IvaylooTs/StarTracker/Docs/Hardware_reasearch/Day 25 - 14.08.md

Optimized the raspberry pi by removing 

systemd-analyze blame
systemd-analyze critical-chain
systemd-analyze

the fasterst optimization was removing this
  sudo systemctl disable NetworkManager-wait-online.service 
this sped up the boot time from ~11 seconds to ~ 5-6 seconds

  sudo systemctl status bluetooth
   sudo systemctl status hciuart
   sudo systemctl deactivate hciuart
   sudo systemctl disable bluetooth

 1334  sudo systemctl disable avahi-daemon
static ip
 1364  sudo systemctl status keyboard-setup.service
 1365  sudo systemctl status triggerhappy.s
 1366  sudo systemctl status triggerhappy
 1367  sudo systemctl status ModemManager.service 
 1368  sudo systemctl status avahi-daemon.s
 1369  sudo systemctl status avahi-daemon.service 
 1370  sudo systemctl status avahi-daemon
 1371  sudo systemctl status dphys-swapfil 1375  sudo systemctl disable rpi-eeprom-update.service 
 1376  sudo systemctl disable keyboard-setup.service 
e.service 
 1372  systemd-analyze 

 1432  sudo systemd-analyze blame
 1433  sudo systemd-analyze time
 1434  sudo cat /sys/kernel/debug/mmc0/ios
 1435  sudo nano /boot/firmware/config.txt 
 1436  reboot
 1437  sudo cat /sys/kernel/debug/mmc0/ios
 1438  sudo nano /boot/firmware/config.txt

other systems
disable_splash=1
boot_delay=0
initial_turbo=30
dtparam=audio=off
dtparam=spi=off
display_auto_detect=0
gpu_mem=16

dtparam=sd_overclock=100 - not used, didn't work.
