IvaylooTs/StarTracker/Docs/Hardware_reasearch/Day 7 - 27.07.md

No significant progress made that day.

Studying quaternions little -> https://eater.net/quaternions/
https://forums.unrealengine.com/t/how-to-use-quaternions/635199

Experimentation with Three.js for visualization of objects with quaternions, transfer information via web sockets.

```html
<!-- used version from day 8 28.07-->
<!DOCTYPE html>
<html>
<head>
<title>WebSocket Test</title>
<style>
	#messages {
		max-height: 400px;
		overflow-y: auto;
		border: 1px solid #ccc;
		padding: 10px;
		font-family: sans-serif;
	}
	#three-container {
		position: absolute;
		top: 0;
		left: 0;
		width: 50vw; /* Half width */
		height: 50vh; /* Half height */
		background: white;
		overflow: hidden;
	}
</style>
</head>
<body>
<h1>Messages from Raspberry Pi:</h1>

<script>
	const ws = new WebSocket('ws://192.168.55.160:6789');
	ws.onopen = () => console.log('WebSocket connected');
	ws.onmessage = function(event) {
		const messageDiv = document.getElementById('messages');
		const p = document.createElement('p');
		p.textContent = event.data;
		messageDiv.appendChild(p);
		messageDiv.scrollTop = messageDiv.scrollHeight;
	};
	
	ws.onclose = () => console.log('WebSocket closed');
	ws.onerror = (err) => console.error('WebSocket error:', err);
</script>
</body>
</html>
```
