IvaylooTs/StarTracker/backups/First interface/README.md

# Day 9

Finished the front UI 
 - cannot push custom commands from terminal CLI, needs custom buttons
 - 3d visualization
 - quaternion display
 - received info displayed
 - camera live

Raspberry Pi server
 - get data from sensor I2C (no library, direct connection)
 - calibrates on hardware level
 - gets camera live video (VGA quality - fast video, Full HD - slow video)
