IvaylooTs/StarTracker/CASSI_Website/Team.JPG

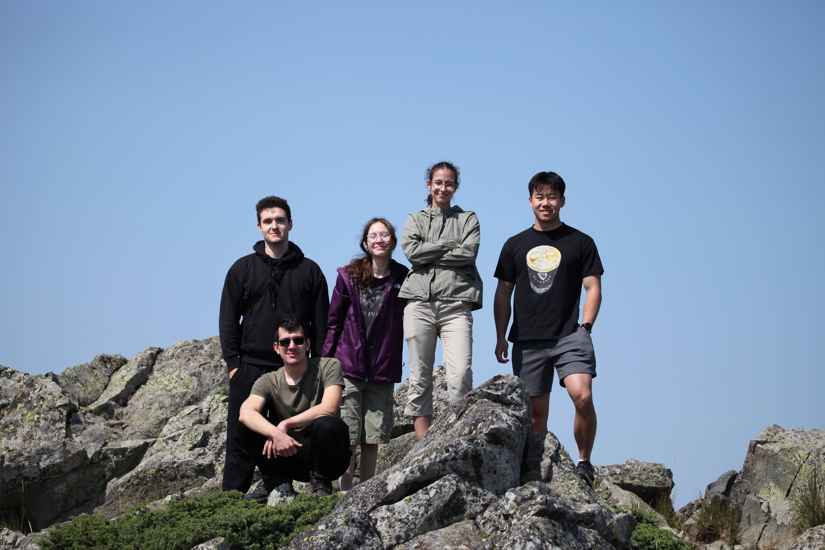
CASSI_Website/Team.JPG
