IvaylooTs/StarTracker/DeveloperUI/Images/wbackground.jpg

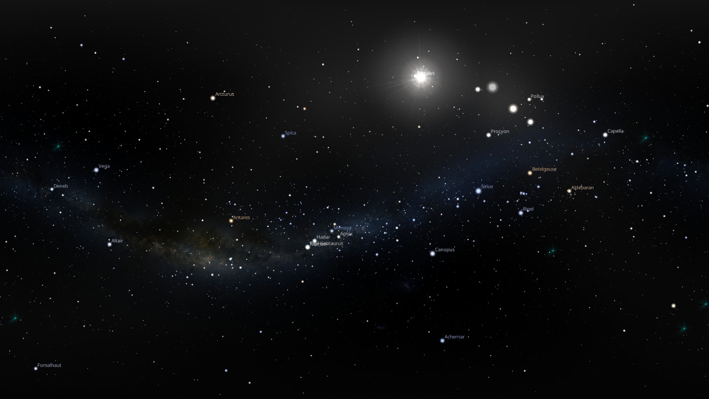
DeveloperUI/Images/wbackground.jpg
