IvaylooTs/StarTracker/DeveloperUI/Pasted image.png

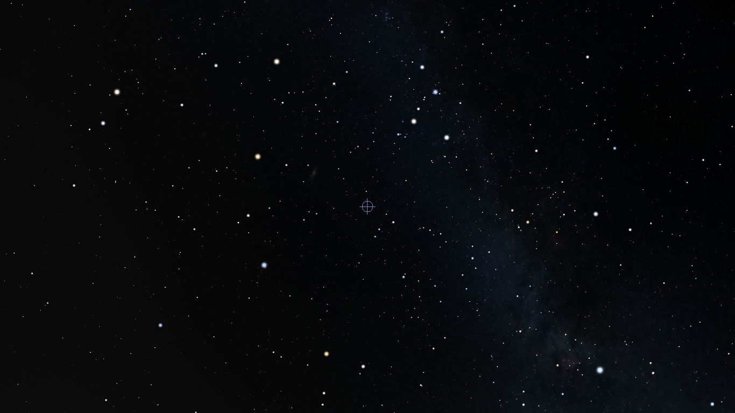
DeveloperUI/Pasted image.png
