IvaylooTs/StarTracker/Docs/Diagrams/BootCycle.drawio(2).png

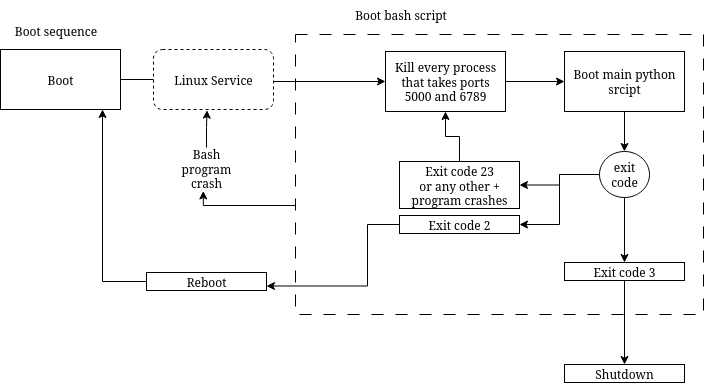
Docs/Diagrams/BootCycle.drawio(2).png
