IvaylooTs/StarTracker/Docs/Diagrams/concept_IMUbootSequence.drawio.png

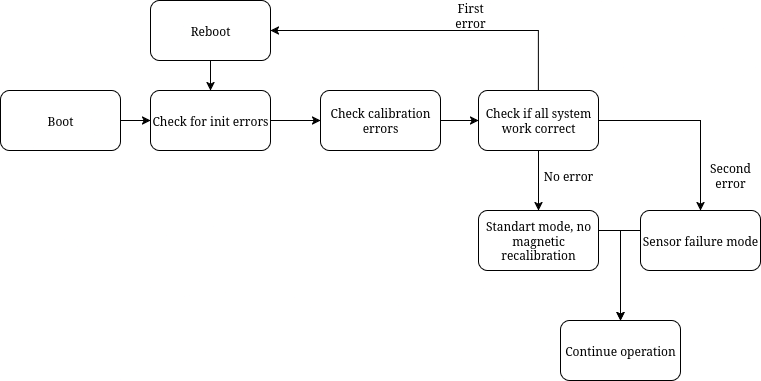
Docs/Diagrams/concept_IMUbootSequence.drawio.png
