IvaylooTs/StarTracker/Docs/Diagrams/Hardware-Diagram.drawio.png

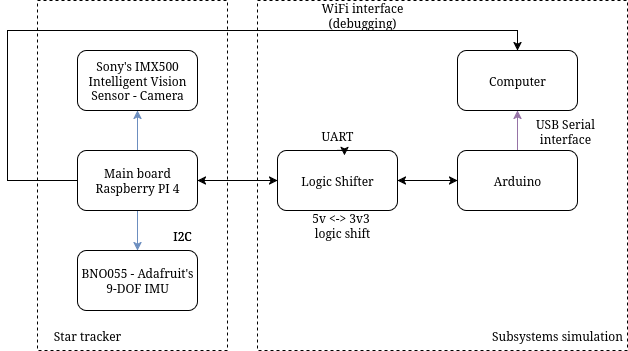
Docs/Diagrams/Hardware-Diagram.drawio.png
