IvaylooTs/StarTracker/Docs/Diagrams/HardwareSystem.drawio.png

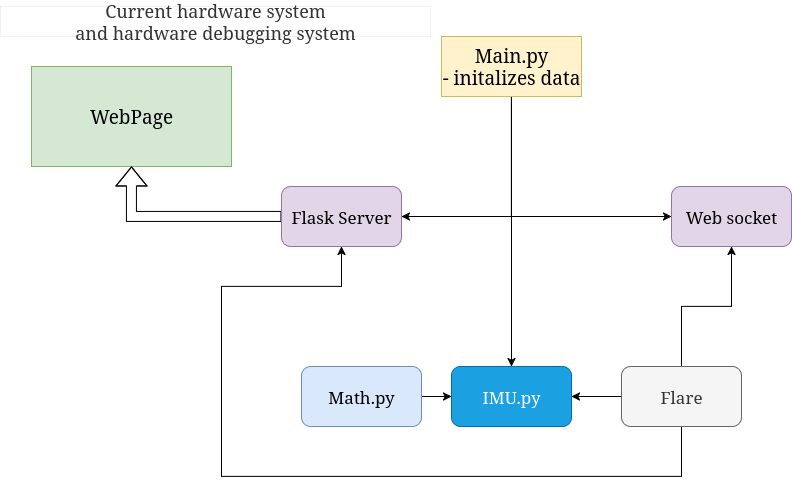
Docs/Diagrams/HardwareSystem.drawio.png
