IvaylooTs/StarTracker/Docs/Hardware_reasearch/additional images/Raspberry Pi Camera connector.png

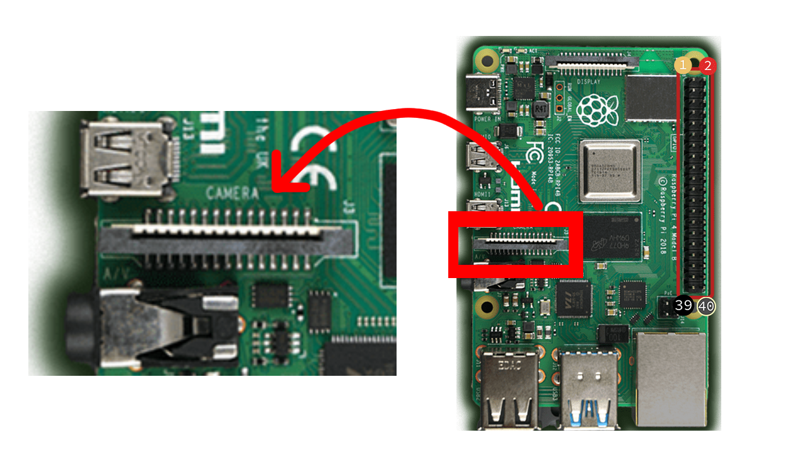
Docs/Hardware_reasearch/additional images/Raspberry Pi Camera connector.png
