IvaylooTs/StarTracker/Docs/Hardware_reasearch/ConceptUI.drawio.png

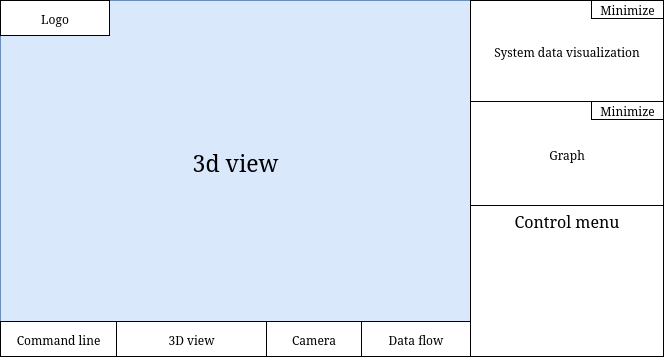
Docs/Hardware_reasearch/ConceptUI.drawio.png
