IvaylooTs/StarTracker/Docs/Hardware_reasearch/Figure_1(1).png

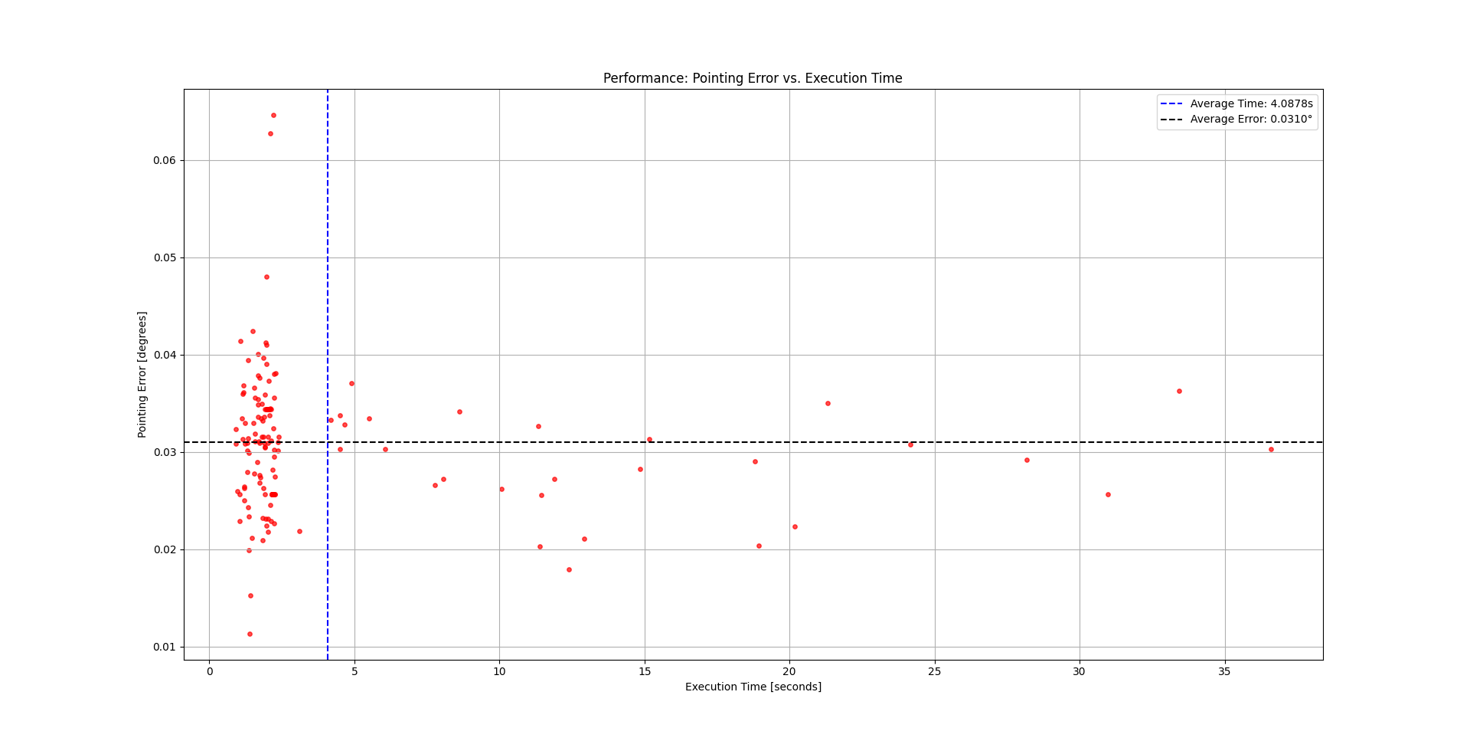
Docs/Hardware_reasearch/Figure_1(1).png
