IvaylooTs/StarTracker/Docs/Hardware_reasearch/Pasted image 20250724163324.png

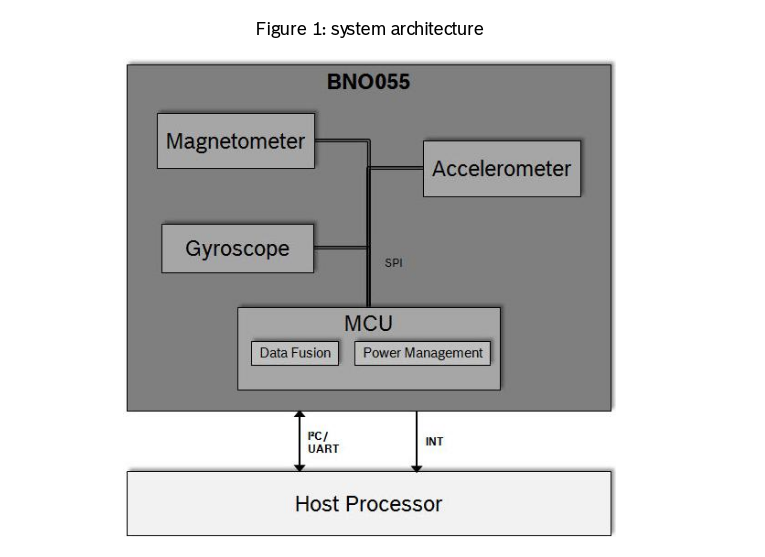
Docs/Hardware_reasearch/Pasted image 20250724163324.png
