IvaylooTs/StarTracker/Docs/Hardware_reasearch/Pasted image 20250725143316.png

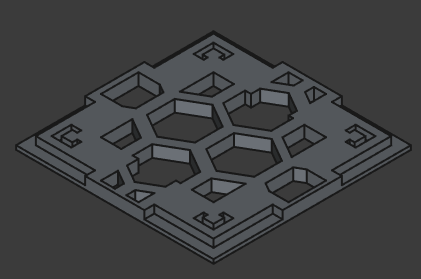
Docs/Hardware_reasearch/Pasted image 20250725143316.png
