IvaylooTs/StarTracker/Docs/Hardware_reasearch/Pasted image 20250729213933.png

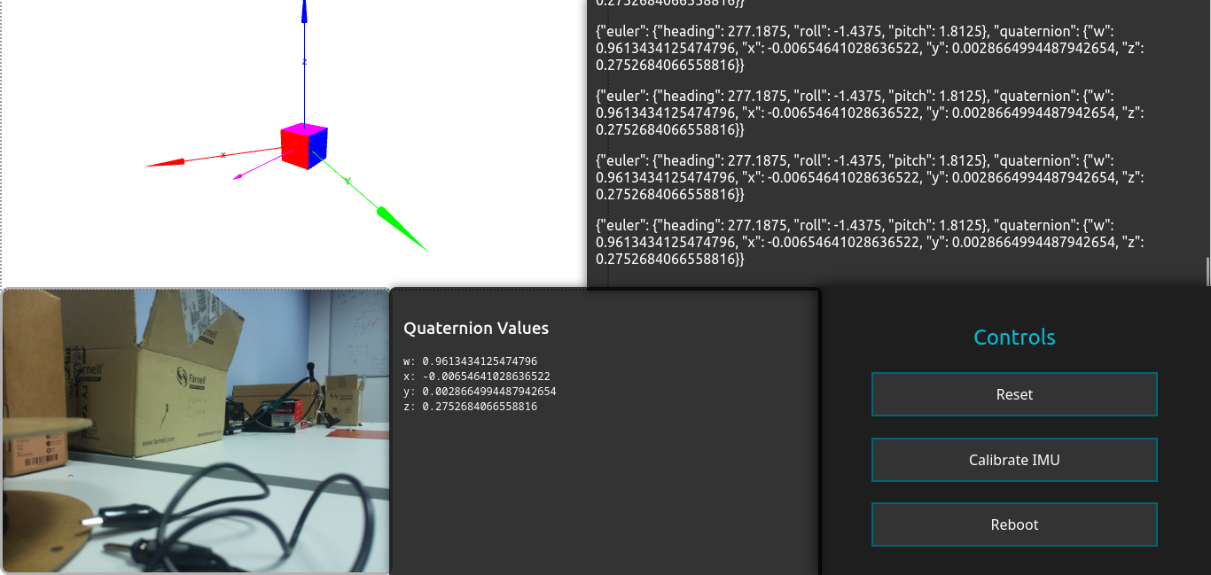
Docs/Hardware_reasearch/Pasted image 20250729213933.png
