IvaylooTs/StarTracker/Docs/Hardware_reasearch/Pasted image 20250731134919.png

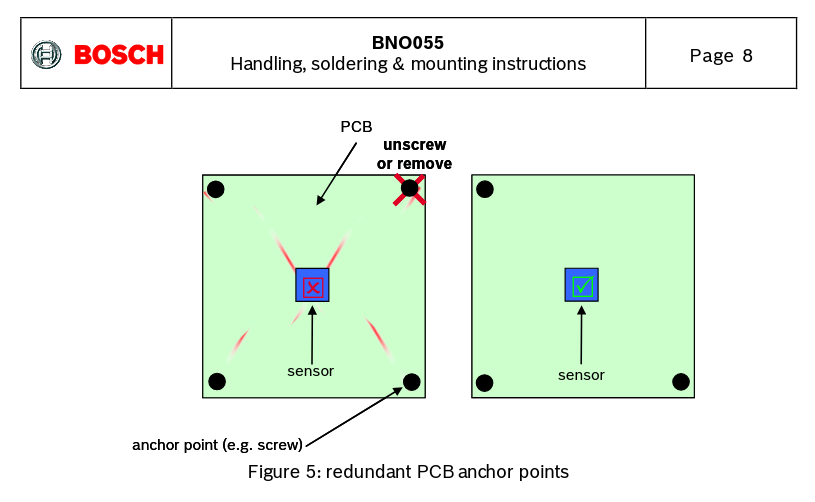
Docs/Hardware_reasearch/Pasted image 20250731134919.png
