IvaylooTs/StarTracker/Docs/Hardware_reasearch/Pasted image 20250815011902.png

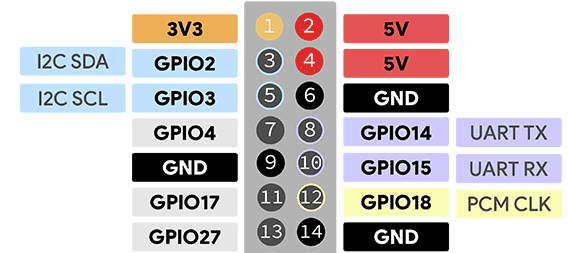
Docs/Hardware_reasearch/Pasted image 20250815011902.png
