IvaylooTs/StarTracker/Docs/Hardware_reasearch/Pasted image 20250816113234.png

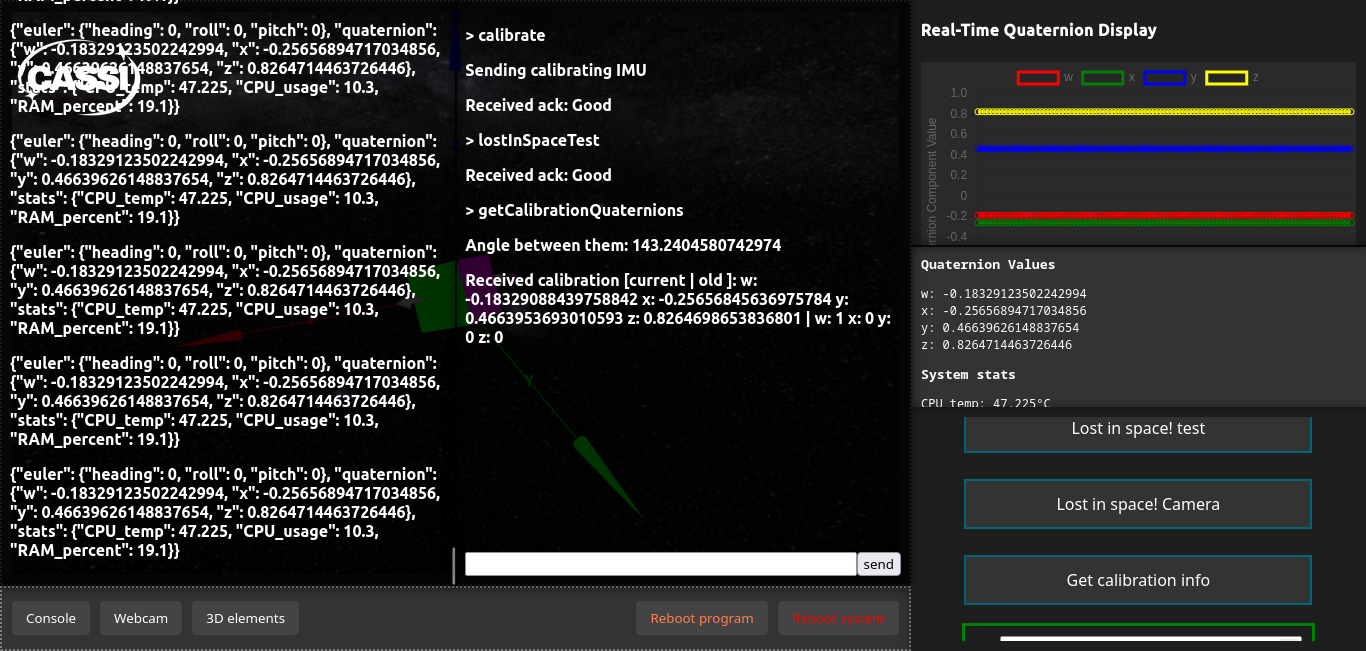
Docs/Hardware_reasearch/Pasted image 20250816113234.png
