IvaylooTs/StarTracker/Docs/Hardware_reasearch/Pasted image 20250816114603.png

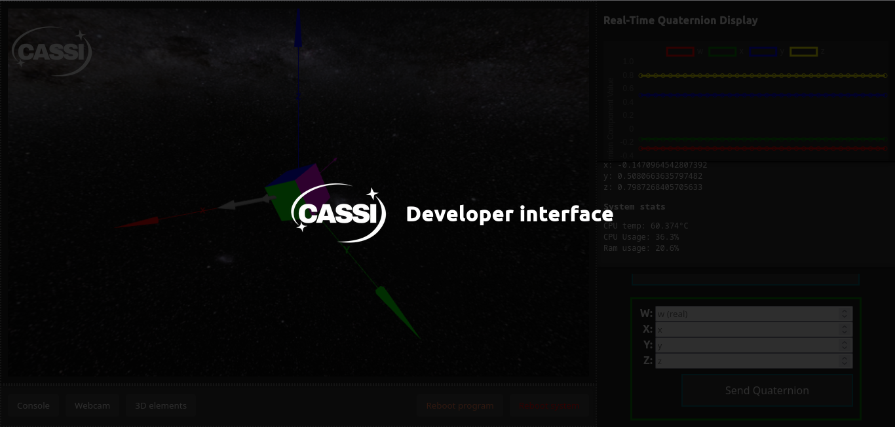
Docs/Hardware_reasearch/Pasted image 20250816114603.png
