IvaylooTs/StarTracker/Docs/Hardware_reasearch/Pasted image 20250816114728.png

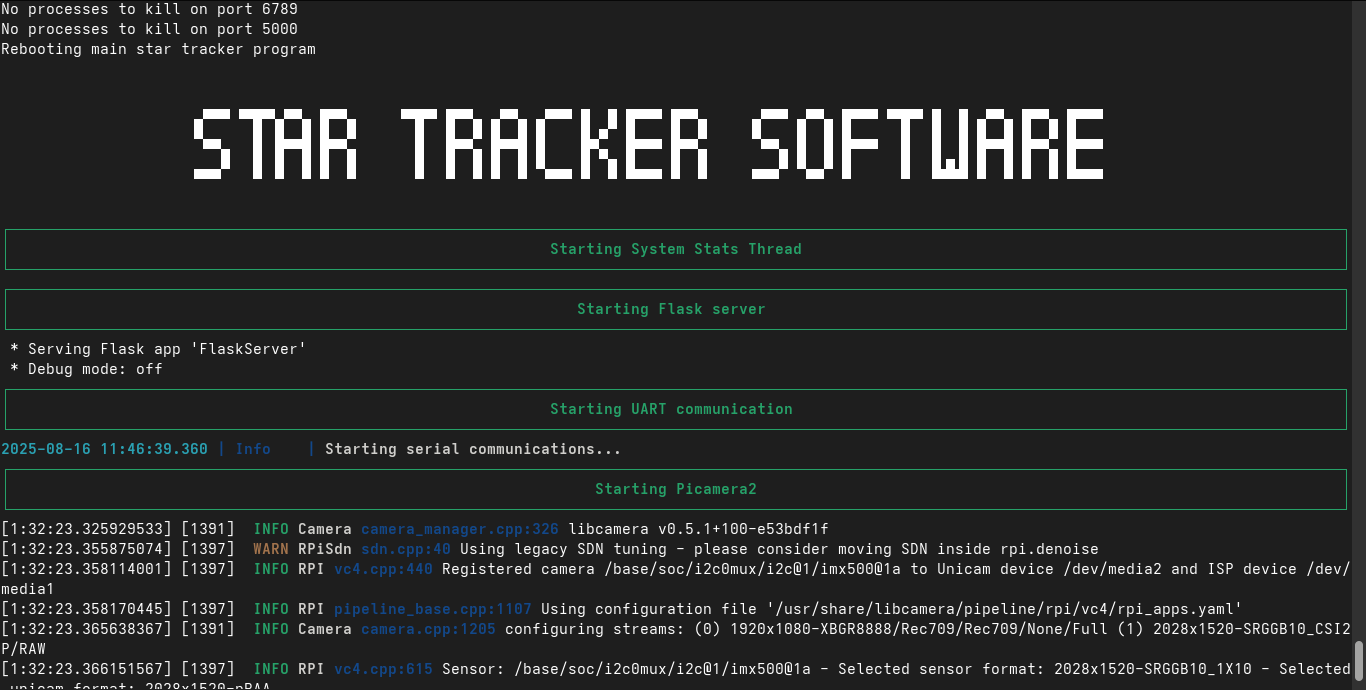
Docs/Hardware_reasearch/Pasted image 20250816114728.png
