IvaylooTs/StarTracker/Docs/Hardware_reasearch/Pasted image 20250816114743.png

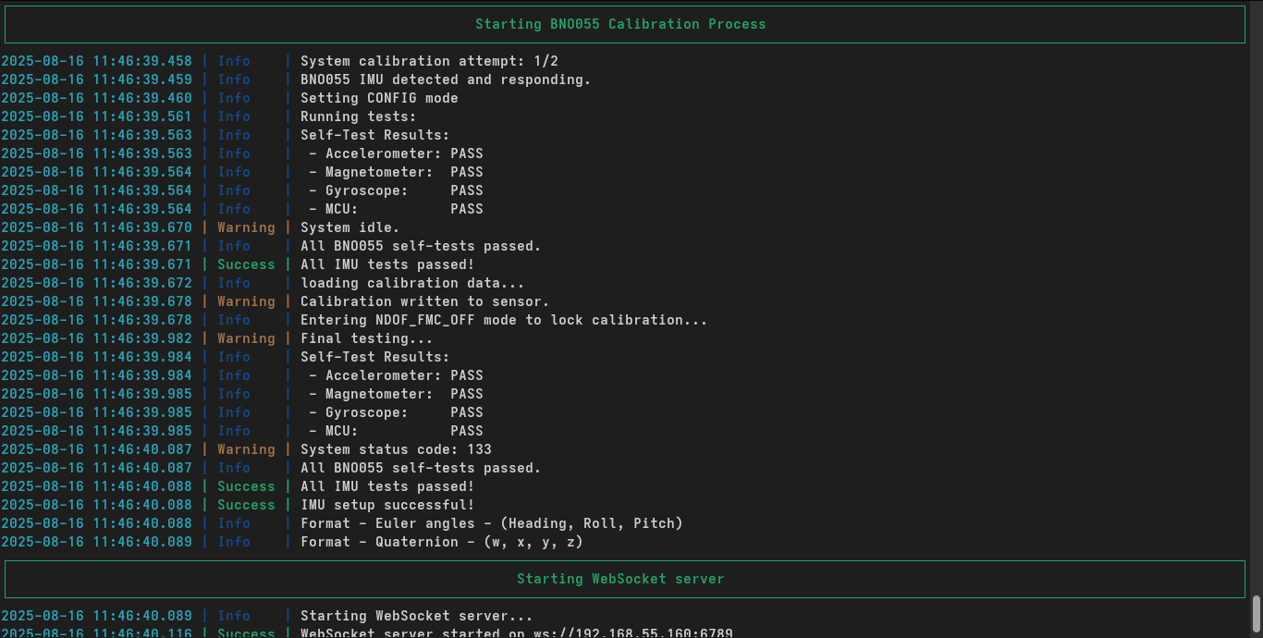
Docs/Hardware_reasearch/Pasted image 20250816114743.png
