IvaylooTs/StarTracker/Docs/Hardware_reasearch/Pasted image 20250816114801.png

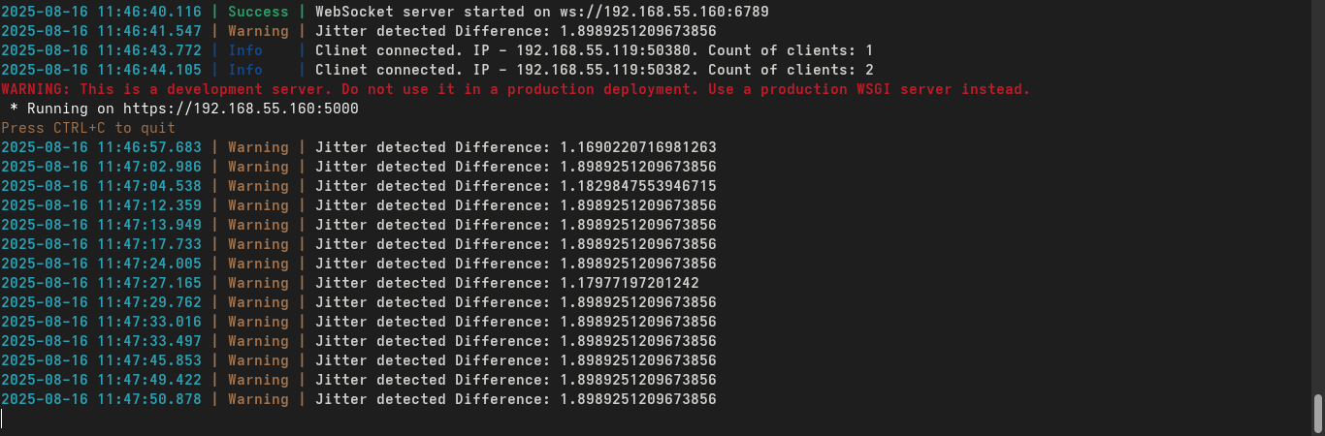
Docs/Hardware_reasearch/Pasted image 20250816114801.png
