IvaylooTs/StarTracker/Docs/Hardware_reasearch/Pasted image 20250816201824.png

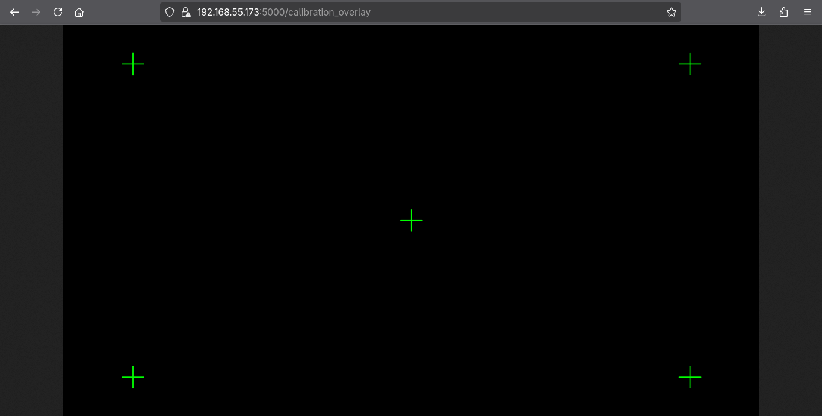
Docs/Hardware_reasearch/Pasted image 20250816201824.png
