IvaylooTs/StarTracker/Docs/Hardware_reasearch/Pasted image 20250816201958.png

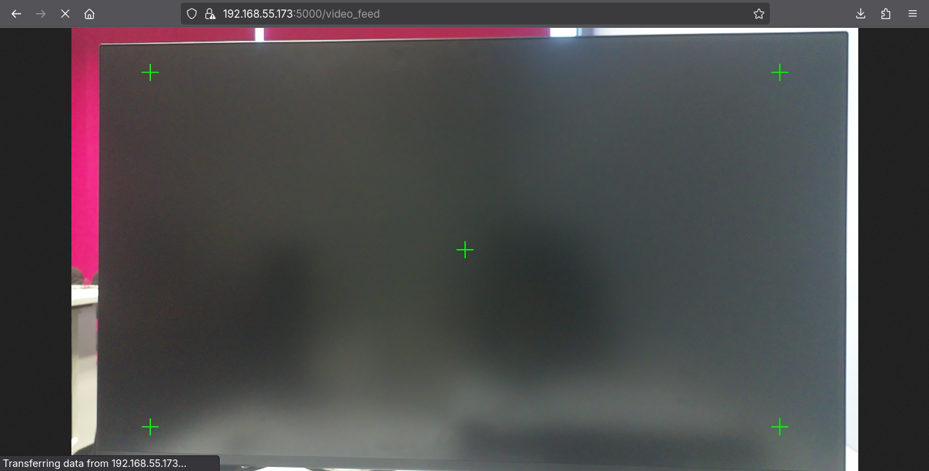
Docs/Hardware_reasearch/Pasted image 20250816201958.png
