IvaylooTs/StarTracker/Docs/Hardware_reasearch/Pasted image 20250816202409.png

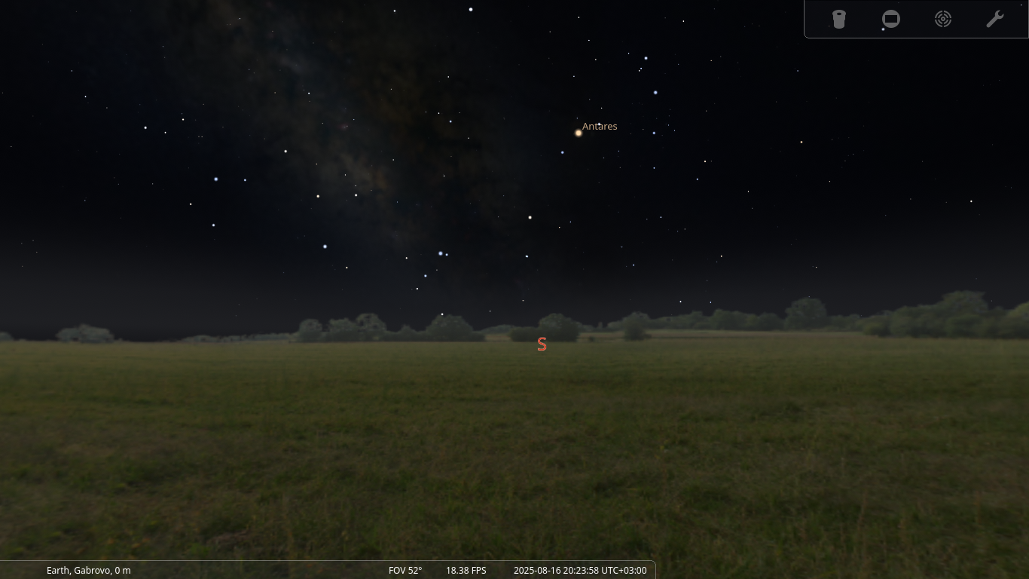
Docs/Hardware_reasearch/Pasted image 20250816202409.png
