IvaylooTs/StarTracker/Docs/Hardware_reasearch/Pasted image 20250816202426.png

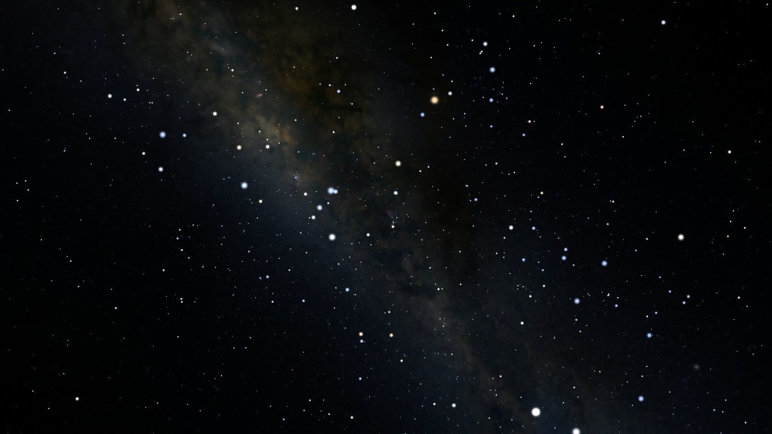
Docs/Hardware_reasearch/Pasted image 20250816202426.png
