IvaylooTs/StarTracker/Docs/Hardware_reasearch/Screenshot 2025-07-29 at 13-58-42 Three.js Cube with Arrow.png

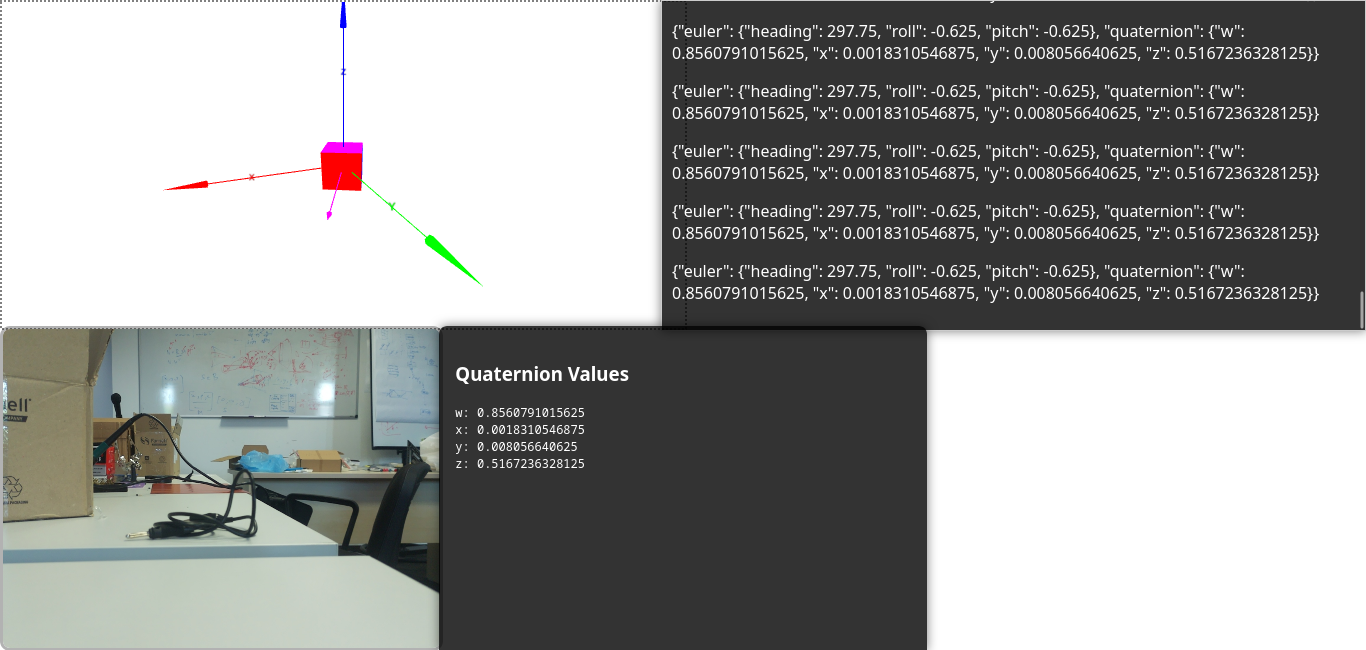
Docs/Hardware_reasearch/Screenshot 2025-07-29 at 13-58-42 Three.js Cube with Arrow.png
