IvaylooTs/StarTracker/Docs/Hardware_reasearch/Screenshot From 2025-07-31 18-01-20.png

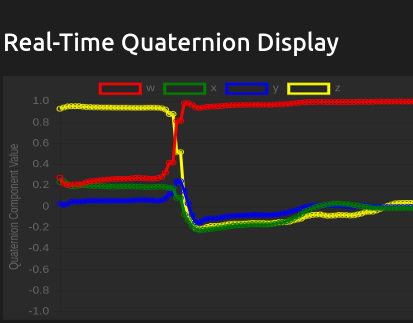
Docs/Hardware_reasearch/Screenshot From 2025-07-31 18-01-20.png
