IvaylooTs/StarTracker/Ivostuff/stars_identified.png

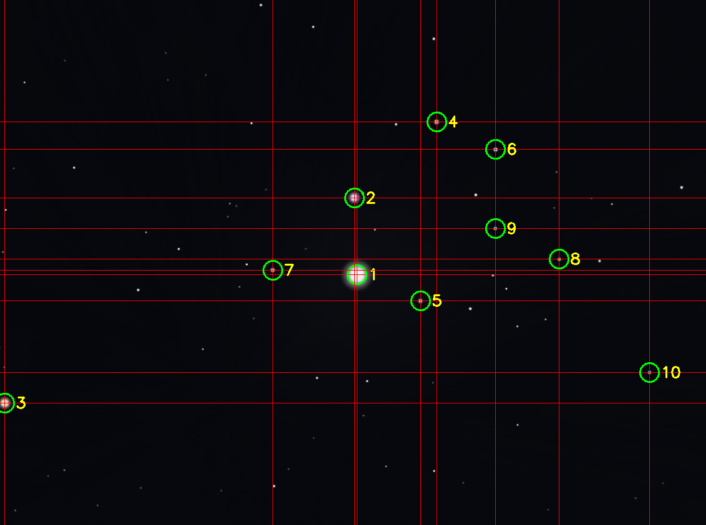
Ivostuff/stars_identified.png
