IvaylooTs/StarTracker/src/digital_twin/script_images/five.png

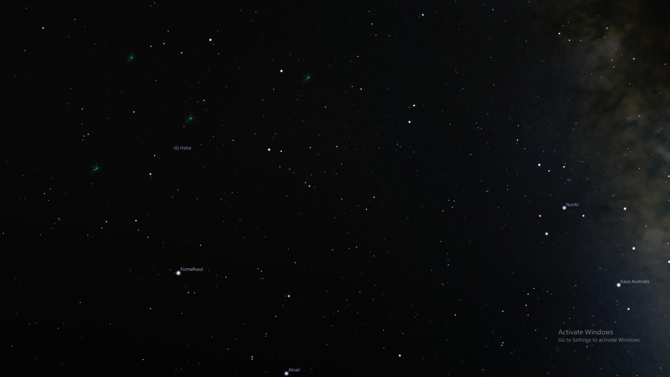
src/digital_twin/script_images/five.png
