IvaylooTs/StarTracker/src/digital_twin/script_images/four.png

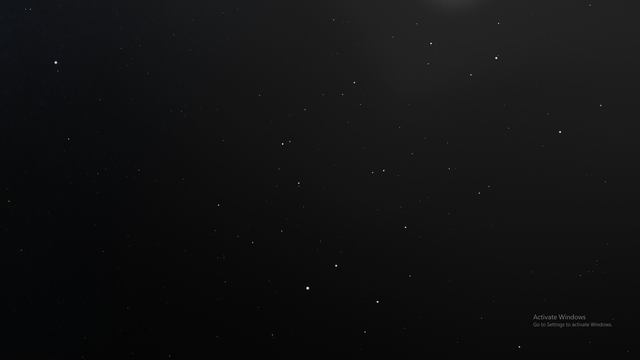
src/digital_twin/script_images/four.png
