IvaylooTs/StarTracker/src/digital_twin/script_images/im2.png

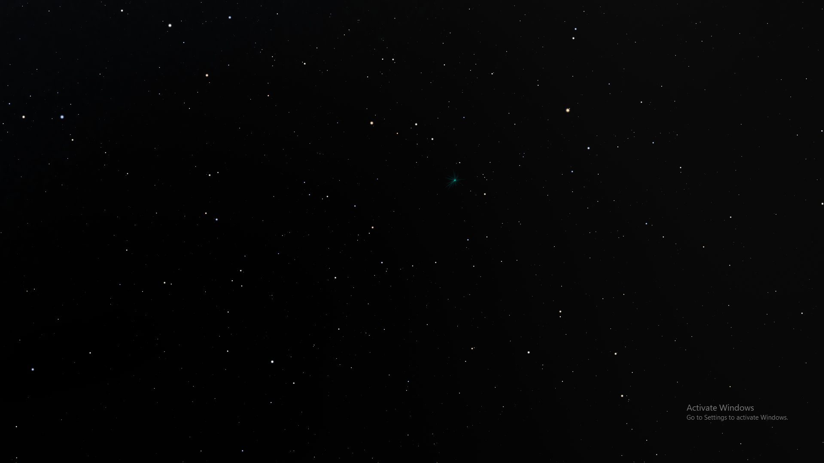
src/digital_twin/script_images/im2.png
