IvaylooTs/StarTracker/src/digital_twin/script_images/im3.png

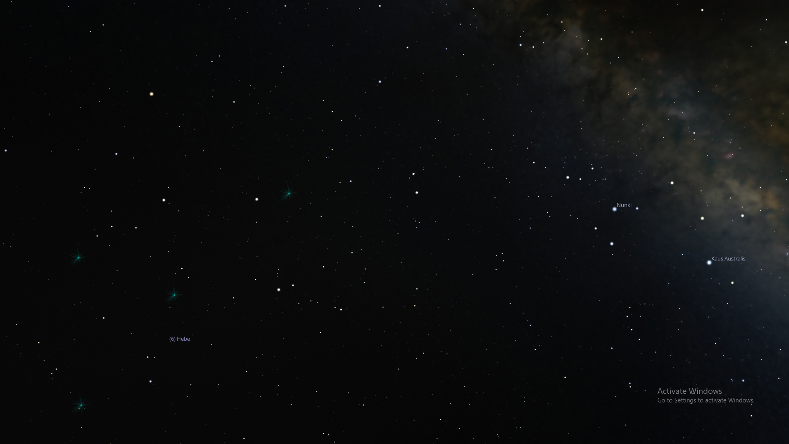
src/digital_twin/script_images/im3.png
