IvaylooTs/StarTracker/src/digital_twin/script_images/image copy.png

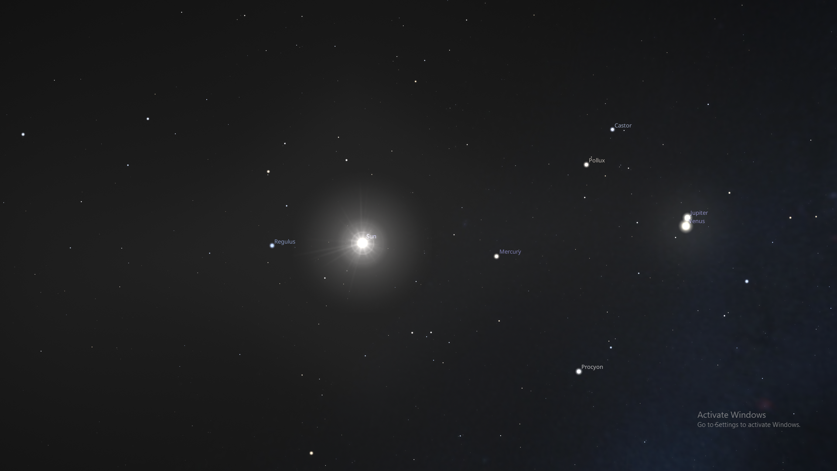
src/digital_twin/script_images/image copy.png
