IvaylooTs/StarTracker/src/digital_twin/script_images/image.png

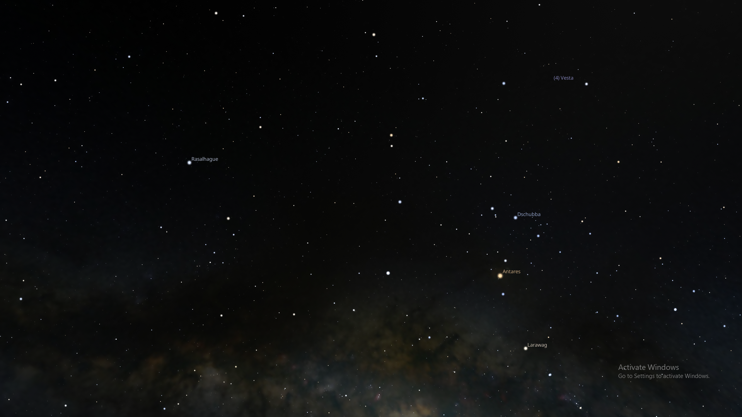
src/digital_twin/script_images/image.png
