IvaylooTs/StarTracker/src/digital_twin/script_images/mars.png

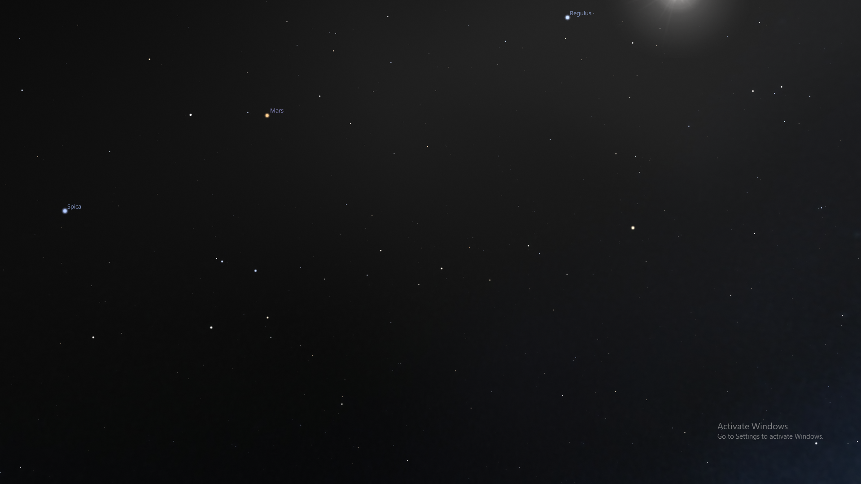
src/digital_twin/script_images/mars.png
