IvaylooTs/StarTracker/src/digital_twin/script_images/one.png

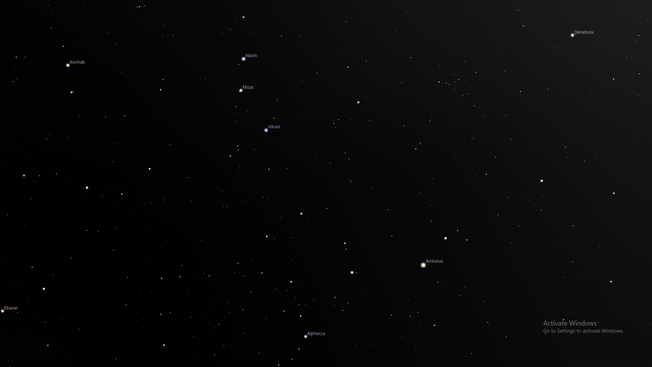
src/digital_twin/script_images/one.png
