IvaylooTs/StarTracker/src/digital_twin/script_images/sat2.png

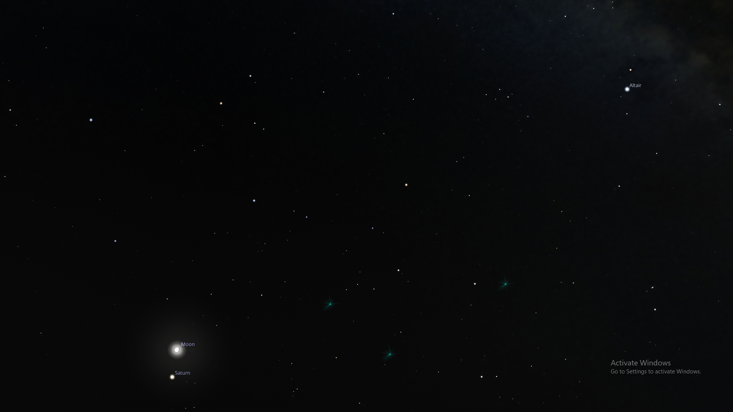
src/digital_twin/script_images/sat2.png
