IvaylooTs/StarTracker/src/digital_twin/script_images/saturn.png

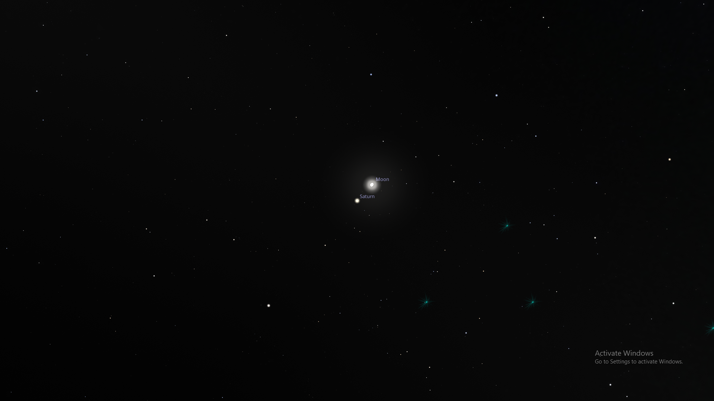
src/digital_twin/script_images/saturn.png
