IvaylooTs/StarTracker/src/digital_twin/script_images/sun.png

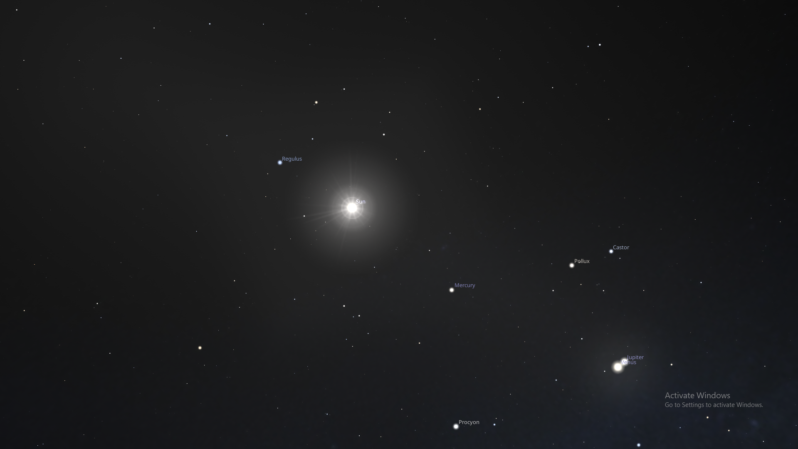
src/digital_twin/script_images/sun.png
