IvaylooTs/StarTracker/src/digital_twin/script_images/three.png

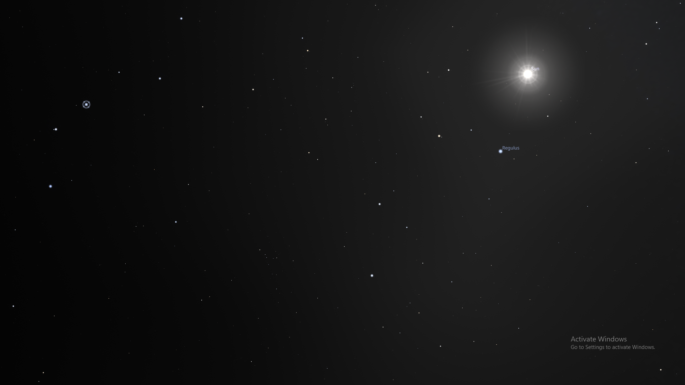
src/digital_twin/script_images/three.png
