IvaylooTs/StarTracker/src/digital_twin/script_images/two.png

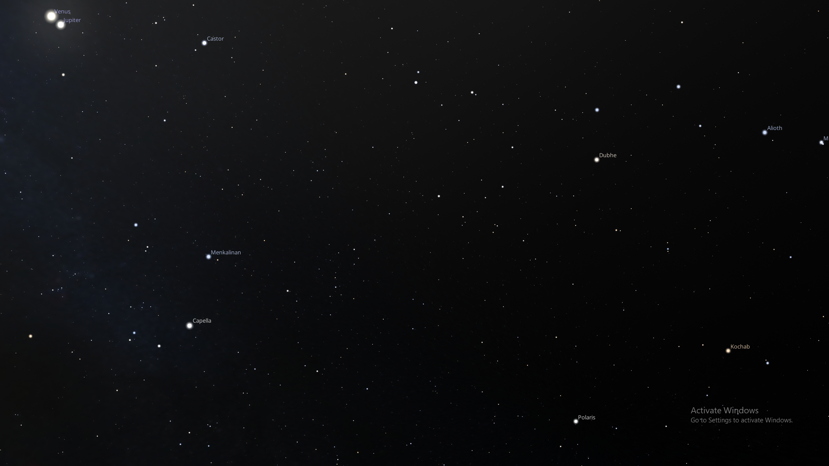
src/digital_twin/script_images/two.png
