IvaylooTs/StarTracker/src/digital_twin/script_images/vertical_045_deg001.png

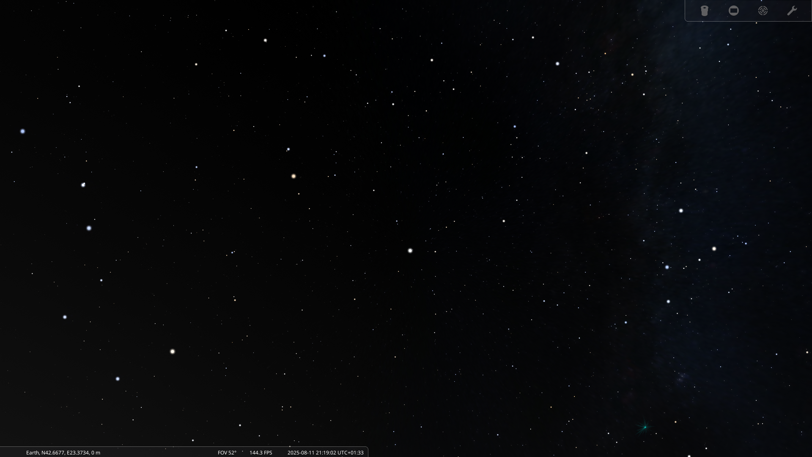
src/digital_twin/script_images/vertical_045_deg001.png
