IvaylooTs/StarTracker/src/digital_twin/script_images/vertical_090_deg001.png

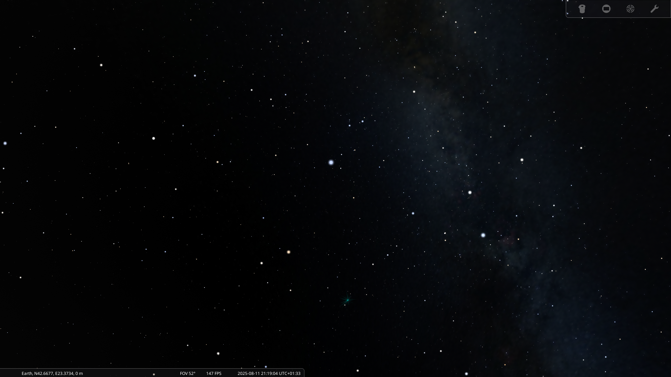
src/digital_twin/script_images/vertical_090_deg001.png
