IvaylooTs/StarTracker/src/digital_twin/script_images/vertical_270_deg001.png

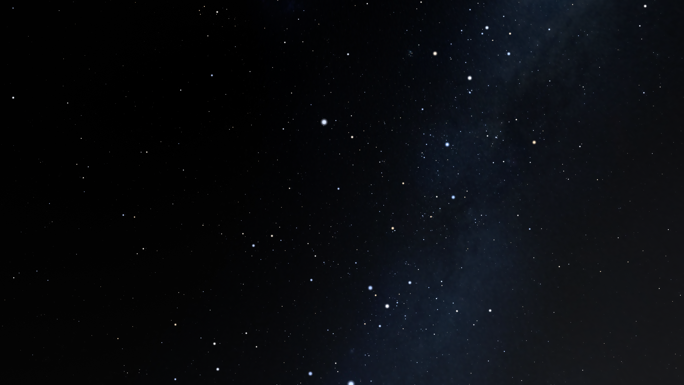
src/digital_twin/script_images/vertical_270_deg001.png
