IvaylooTs/StarTracker/src/digital_twin/script_images/vertical_315_deg001.png

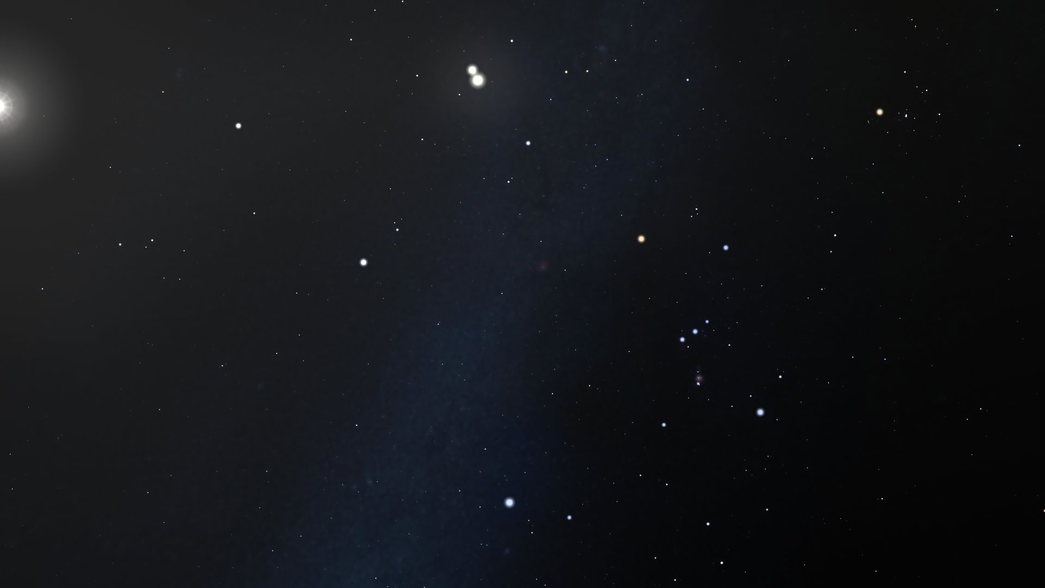
src/digital_twin/script_images/vertical_315_deg001.png
