IvaylooTs/StarTracker/src/digital_twin/stars_identified.png

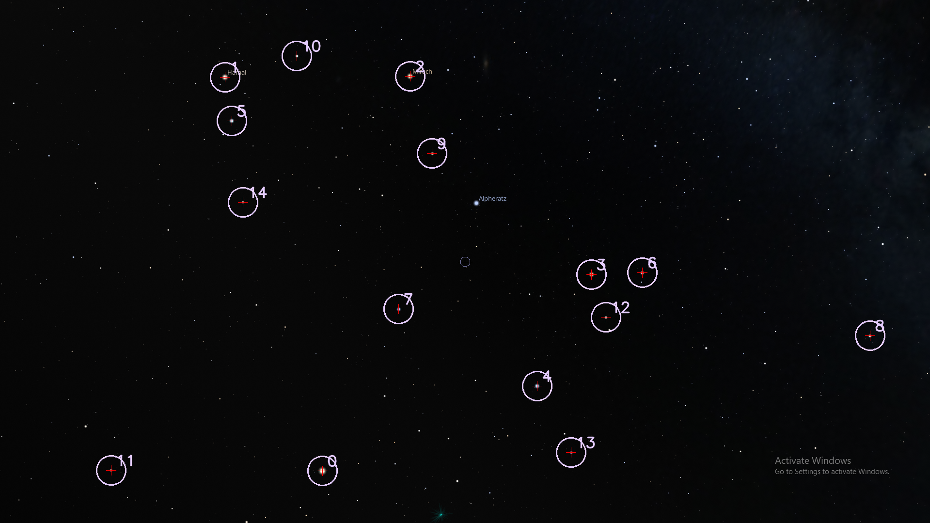
src/digital_twin/stars_identified.png
