IvaylooTs/StarTracker/src/star_tracking/image_processing/stars_identified.png

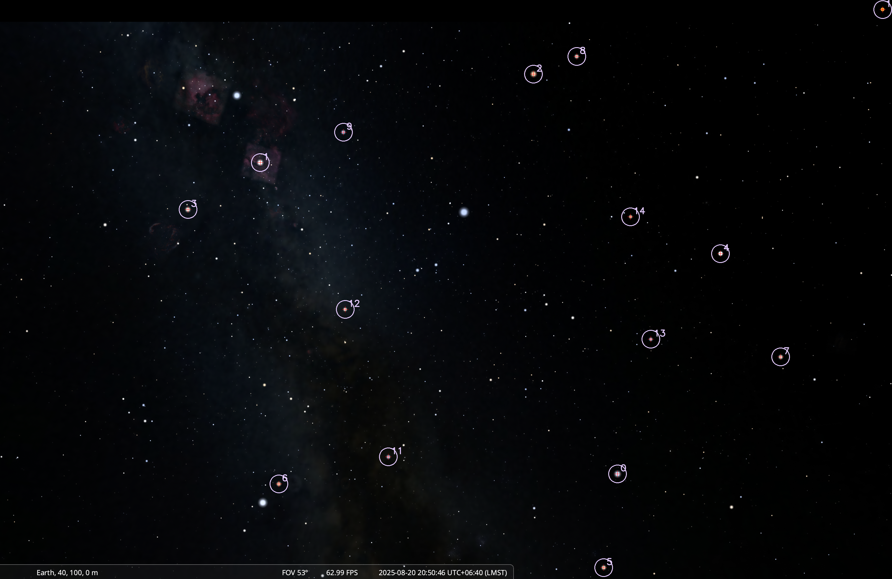
src/star_tracking/image_processing/stars_identified.png
