IvaylooTs/StarTracker/backups/test images from the final/README.md

# info

Some pictures taken on from the star tracker. 
Here you can find some from:
- testing
- presentation
- calibration
