IvaylooTs/StarTracker/Docs/Diagrams/Tests.drawio.png

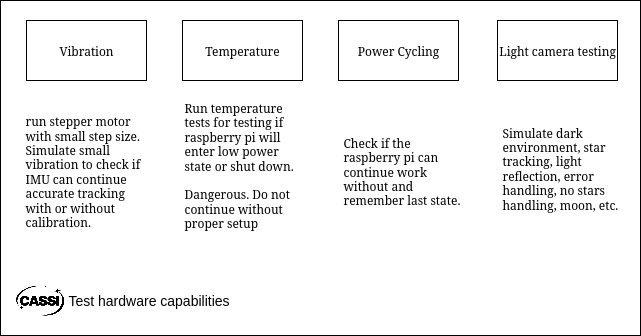
Docs/Diagrams/Tests.drawio.png
