IvaylooTs/StarTracker/src/digital_twin/script_images/test1.png

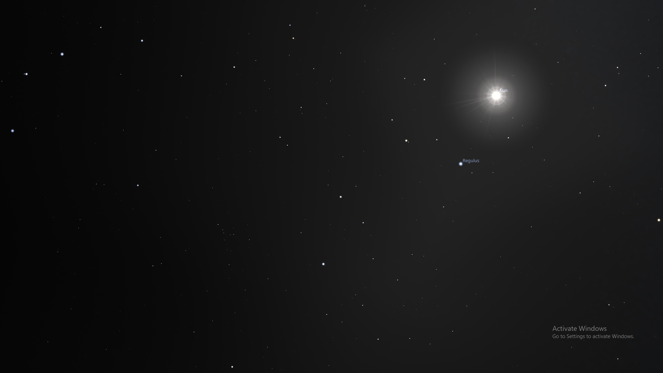
src/digital_twin/script_images/test1.png
