IvaylooTs/StarTracker/src/digital_twin/script_images/test2.png

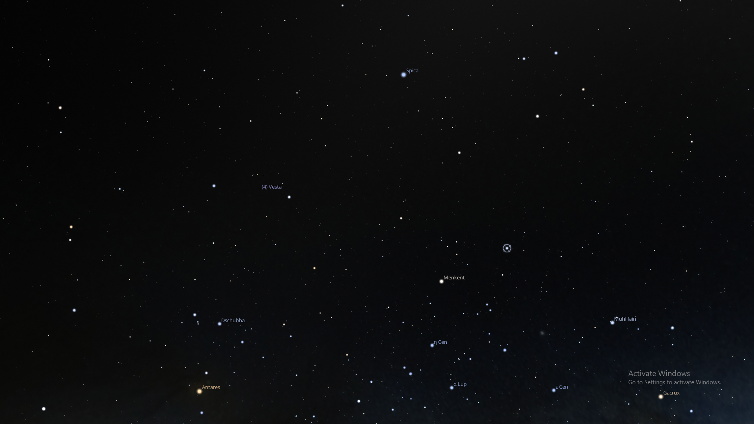
src/digital_twin/script_images/test2.png
