IvaylooTs/StarTracker/src/digital_twin/test_images/cat3.png

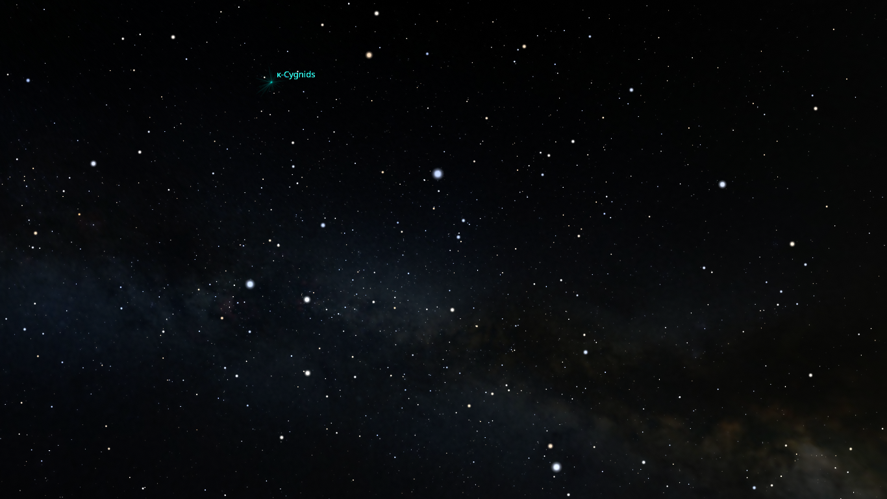
src/digital_twin/test_images/cat3.png
