IvaylooTs/StarTracker/src/digital_twin/test_images/cat5.png

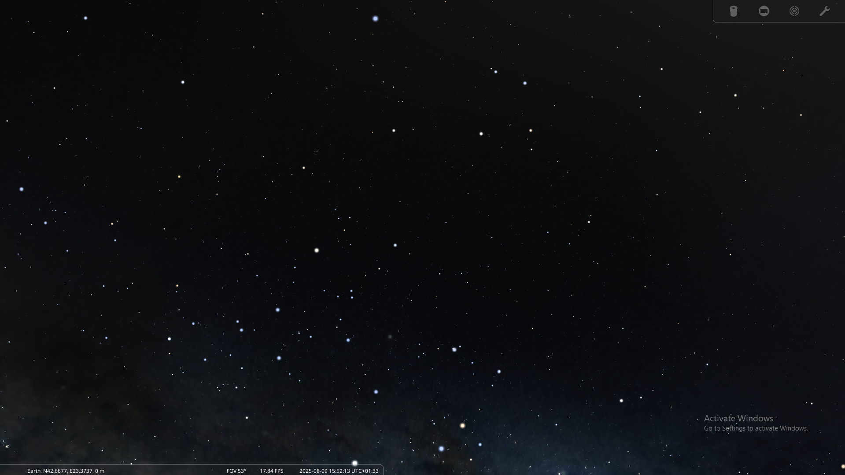
src/digital_twin/test_images/cat5.png
