IvaylooTs/StarTracker/src/digital_twin/test_images/polaris_view_5_FOV.jpeg

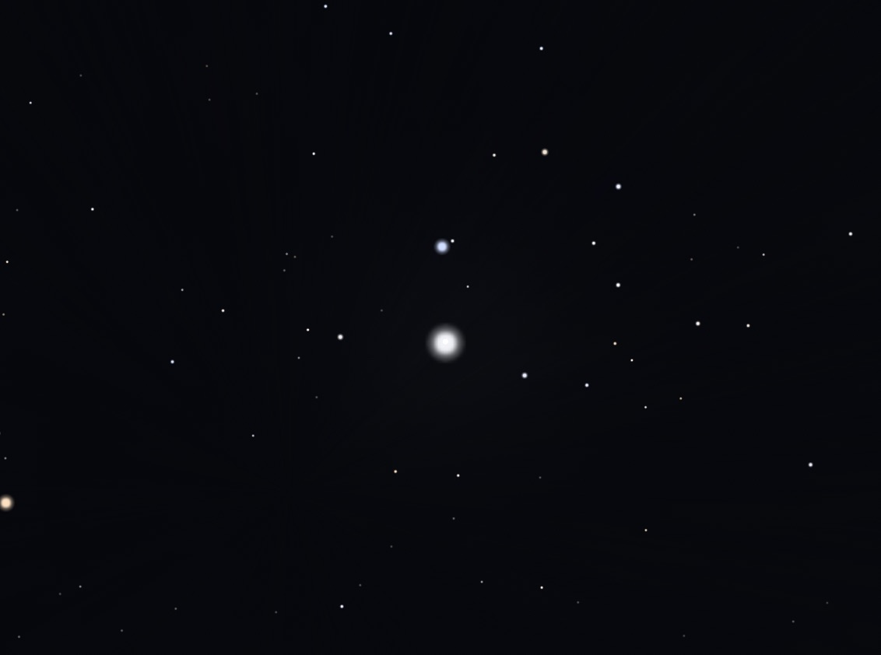
src/digital_twin/test_images/polaris_view_5_FOV.jpeg
