IvaylooTs/StarTracker/src/digital_twin/test_images/saturn2.png

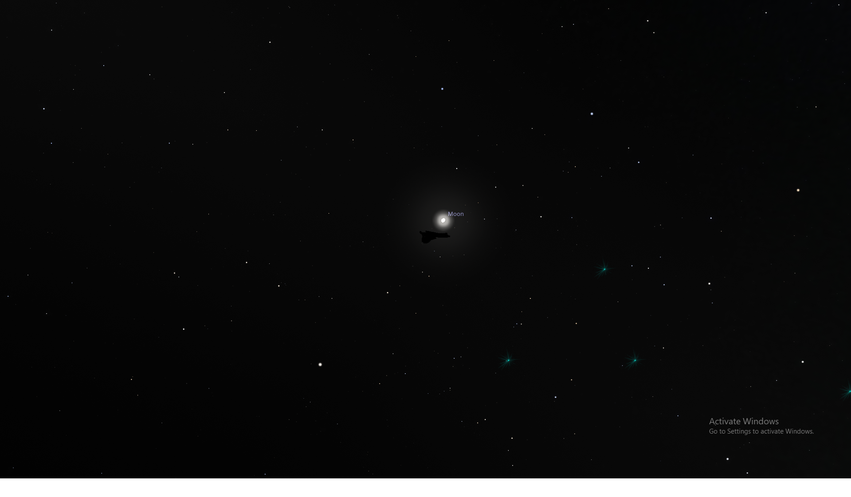
src/digital_twin/test_images/saturn2.png
