IvaylooTs/StarTracker/src/digital_twin/test_images/testing8.png

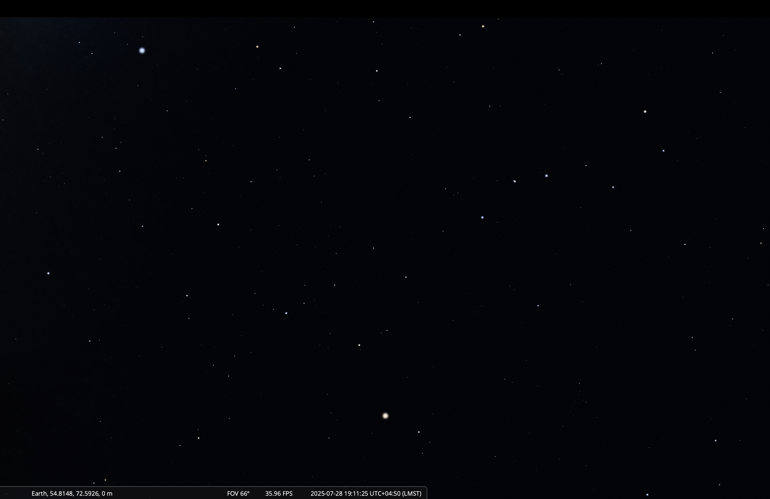
src/digital_twin/test_images/testing8.png
