IvaylooTs/StarTracker/src/digital_twin/test_images/testing11.png

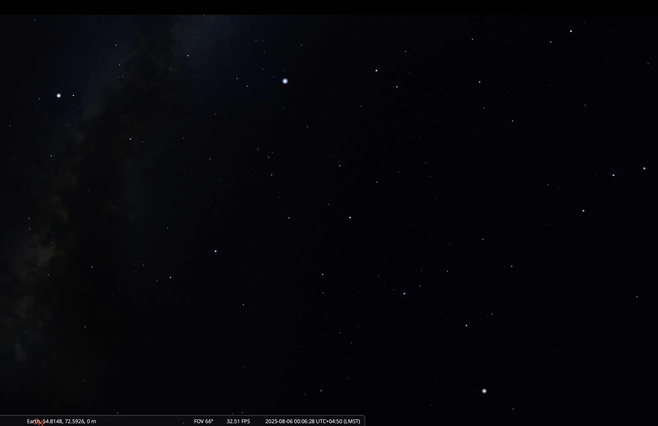
src/digital_twin/test_images/testing11.png
