IvaylooTs/StarTracker/src/digital_twin/test_images/testing18.png

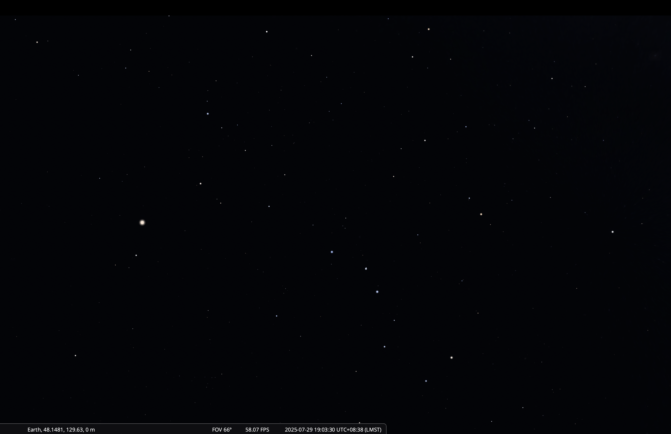
src/digital_twin/test_images/testing18.png
