IvaylooTs/StarTracker/src/digital_twin/test_images/testing23.png

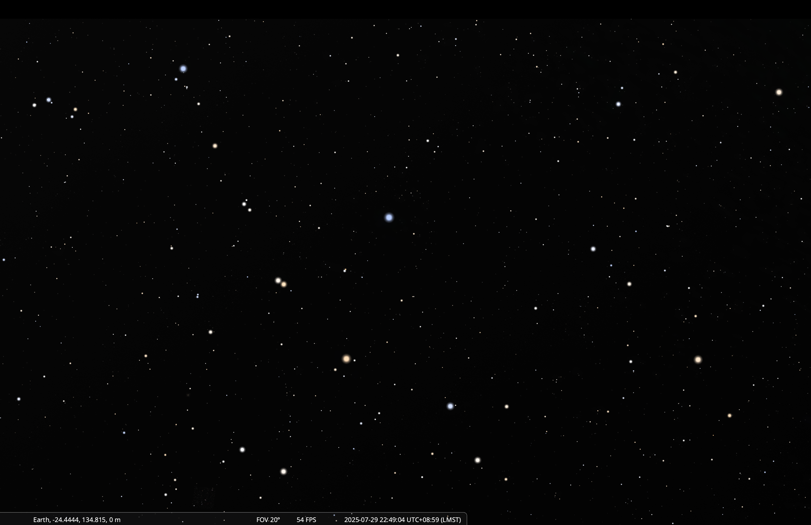
src/digital_twin/test_images/testing23.png
