IvaylooTs/StarTracker/src/digital_twin/test_images/testing24.png

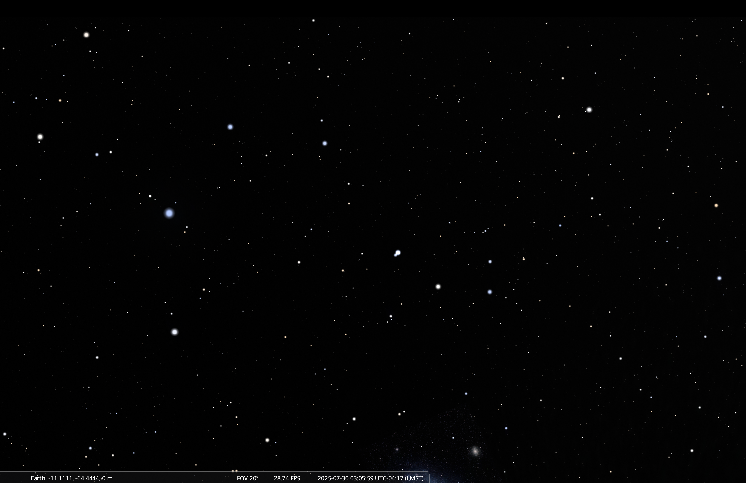
src/digital_twin/test_images/testing24.png
