IvaylooTs/StarTracker/src/digital_twin/test_images/testing27.png

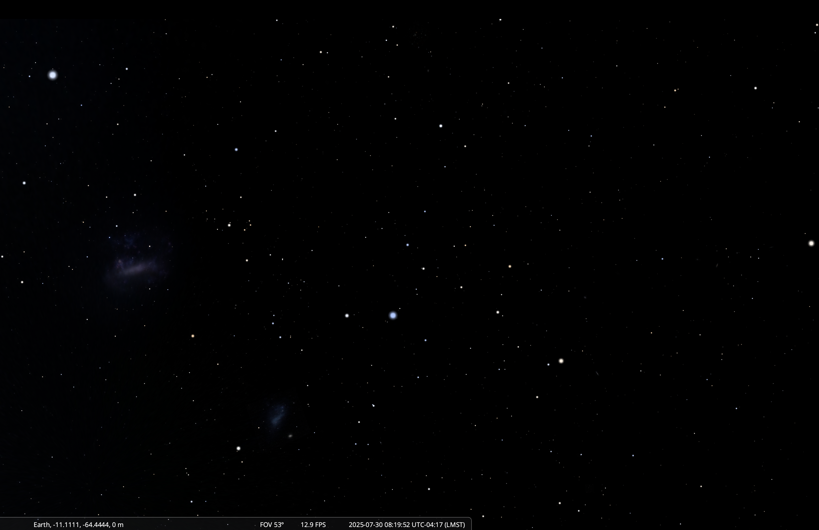
src/digital_twin/test_images/testing27.png
