IvaylooTs/StarTracker/src/digital_twin/test_images/testing29.png

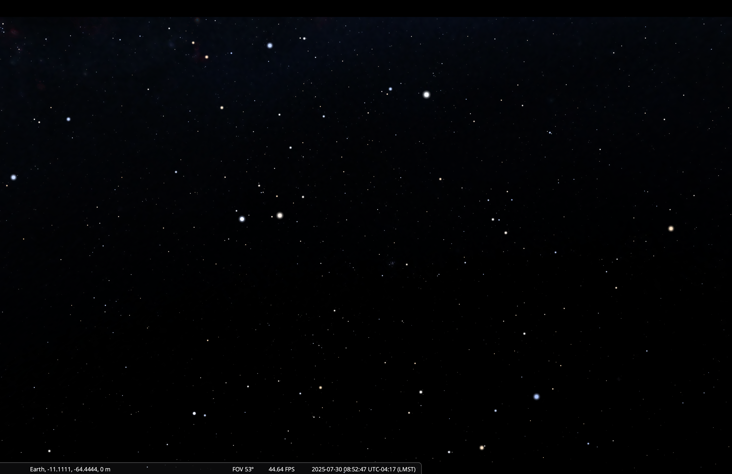
src/digital_twin/test_images/testing29.png
