IvaylooTs/StarTracker/src/digital_twin/test_images/testing34.png

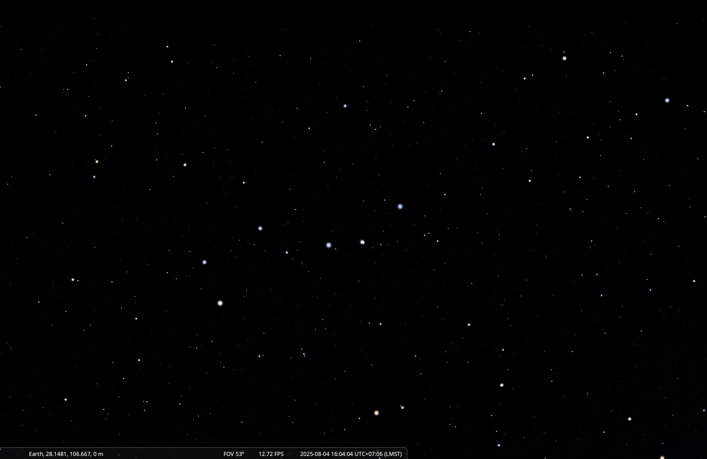
src/digital_twin/test_images/testing34.png
