IvaylooTs/StarTracker/src/digital_twin/test_images/testing35.png

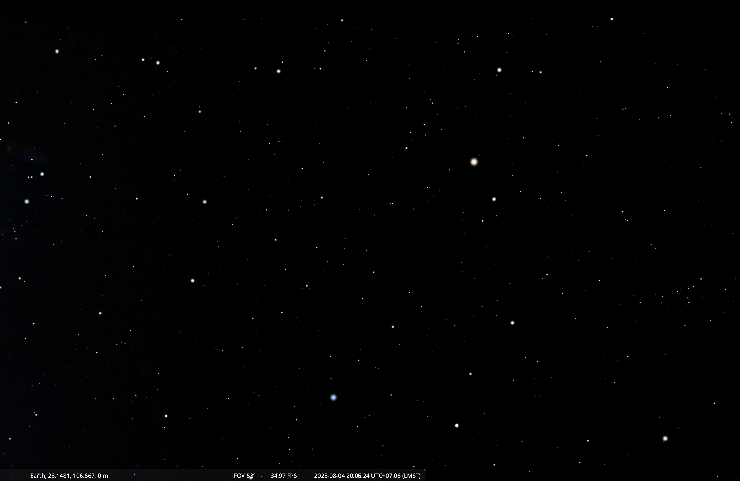
src/digital_twin/test_images/testing35.png
