IvaylooTs/StarTracker/src/digital_twin/test_images/testing37.png

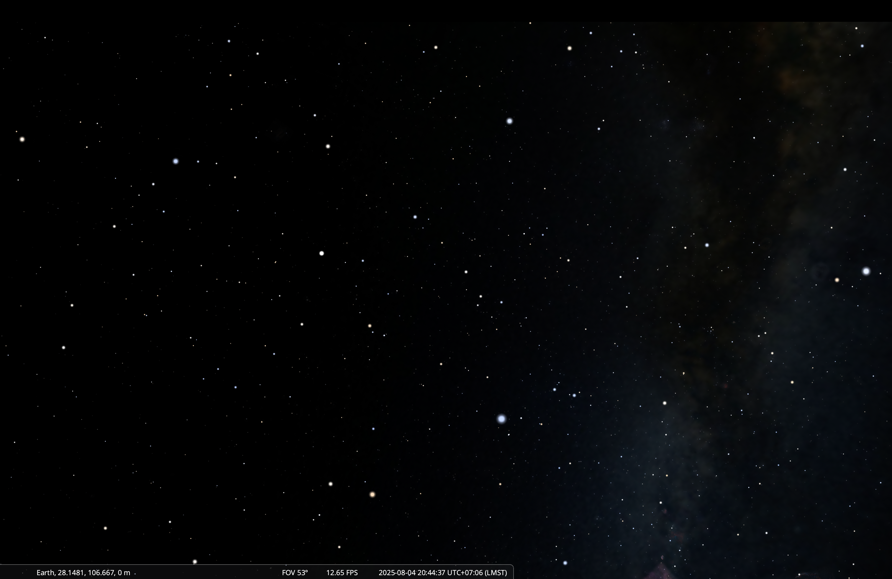
src/digital_twin/test_images/testing37.png
