IvaylooTs/StarTracker/src/digital_twin/test_images/testing38.png

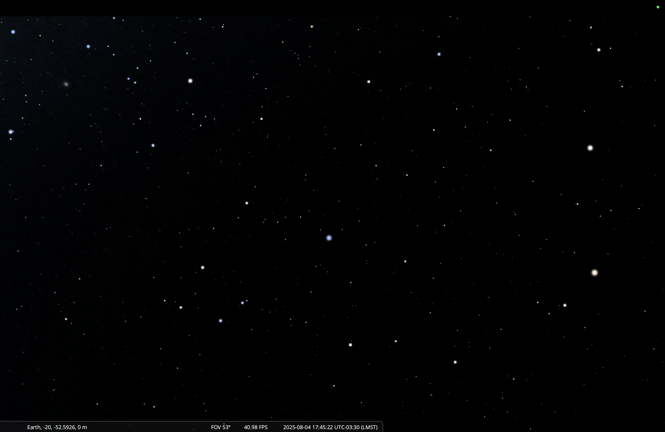
src/digital_twin/test_images/testing38.png
