IvaylooTs/StarTracker/src/digital_twin/test_images/testing39.png

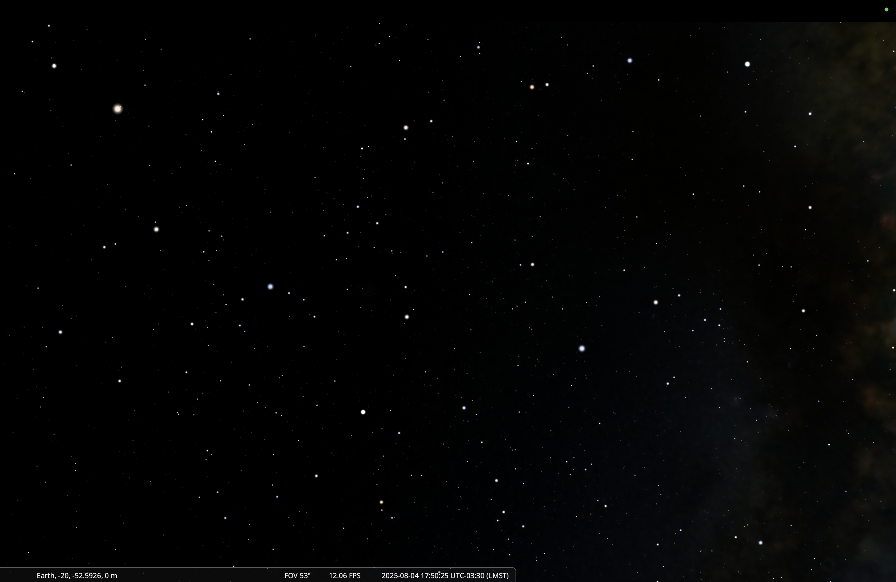
src/digital_twin/test_images/testing39.png
