IvaylooTs/StarTracker/src/digital_twin/test_images/testing40.png

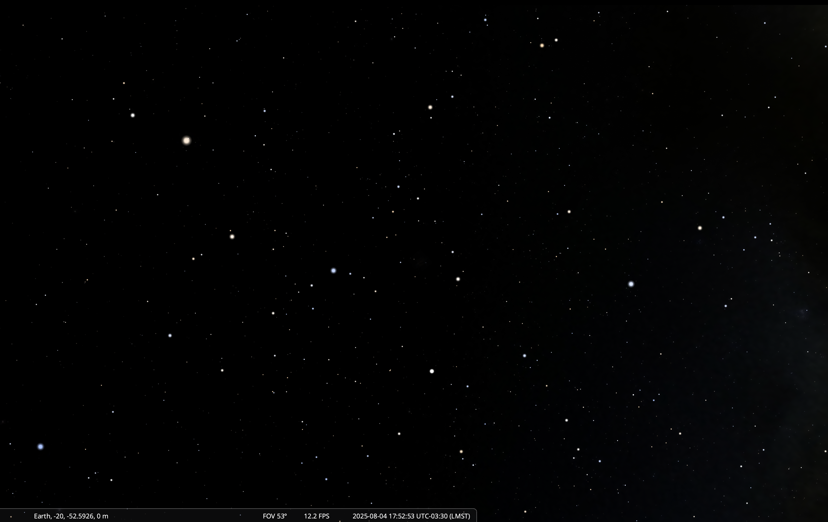
src/digital_twin/test_images/testing40.png
