IvaylooTs/StarTracker/src/digital_twin/test_images/testing43.png

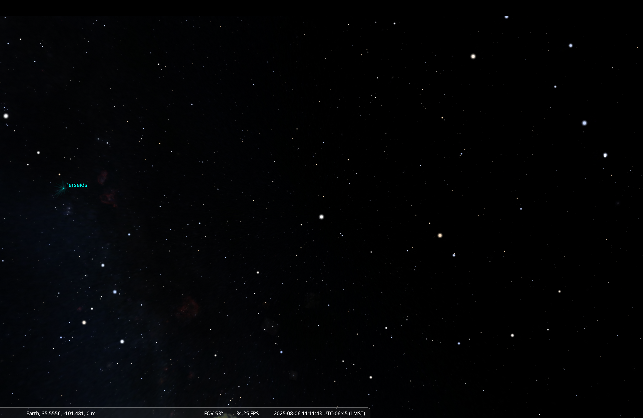
src/digital_twin/test_images/testing43.png
