IvaylooTs/StarTracker/src/digital_twin/test_images/testing44.png

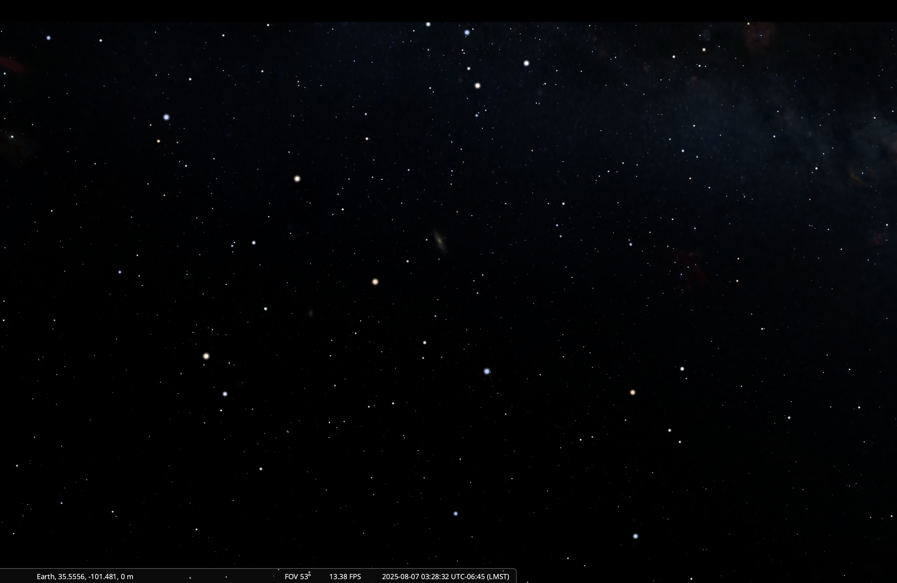
src/digital_twin/test_images/testing44.png
