IvaylooTs/StarTracker/src/digital_twin/test_images/testing45.png

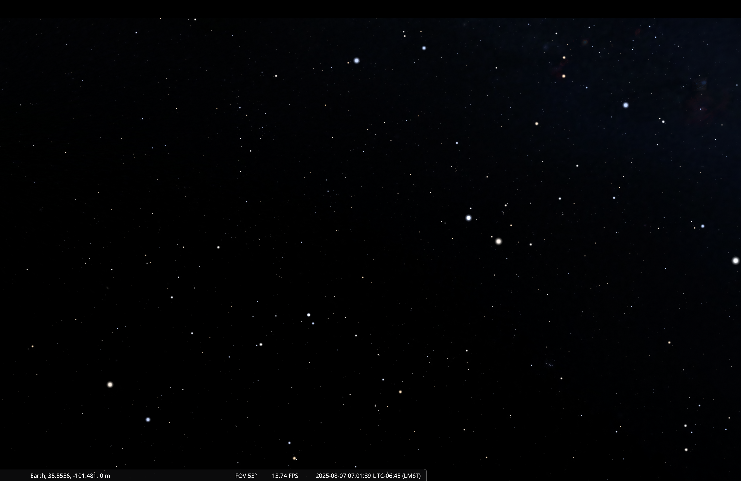
src/digital_twin/test_images/testing45.png
