IvaylooTs/StarTracker/src/digital_twin/test_images/testing46.png

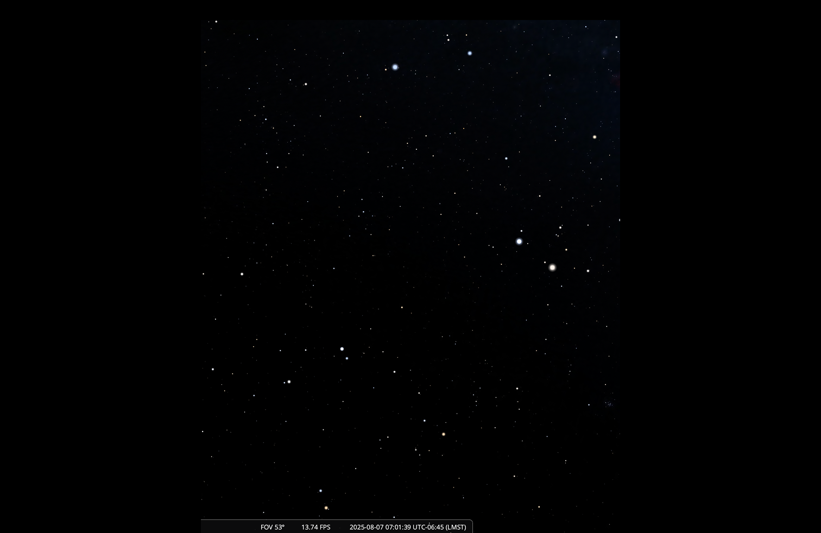
src/digital_twin/test_images/testing46.png
