IvaylooTs/StarTracker/src/digital_twin/test_images/testing47.png

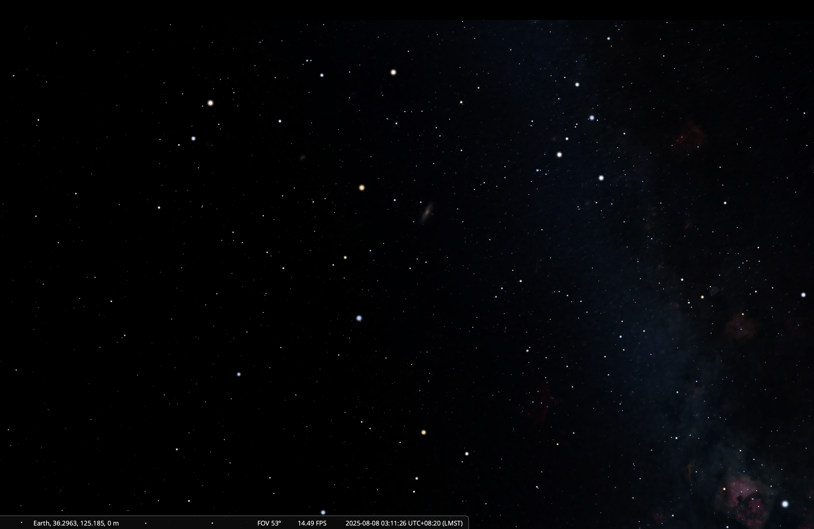
src/digital_twin/test_images/testing47.png
