IvaylooTs/StarTracker/src/digital_twin/test_images/testing48.png

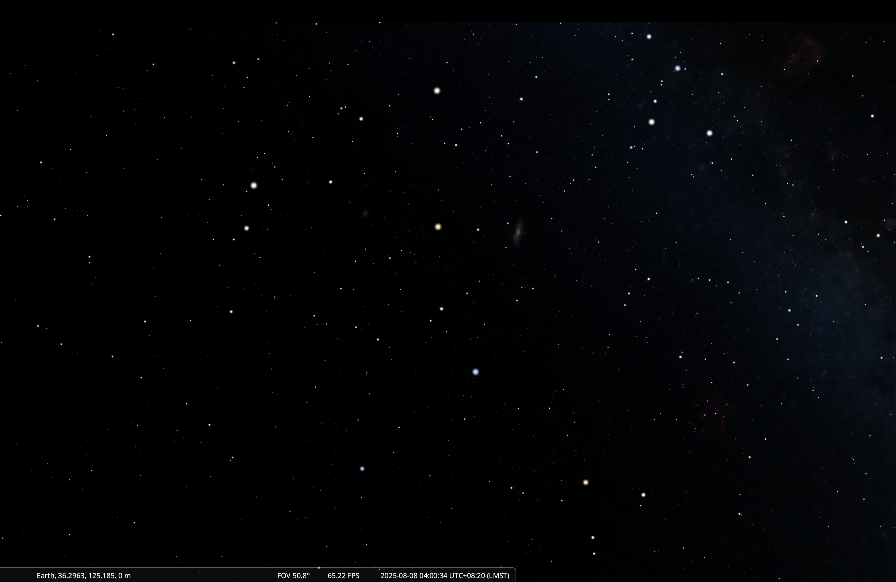
src/digital_twin/test_images/testing48.png
