IvaylooTs/StarTracker/src/digital_twin/test_images/testing50.png

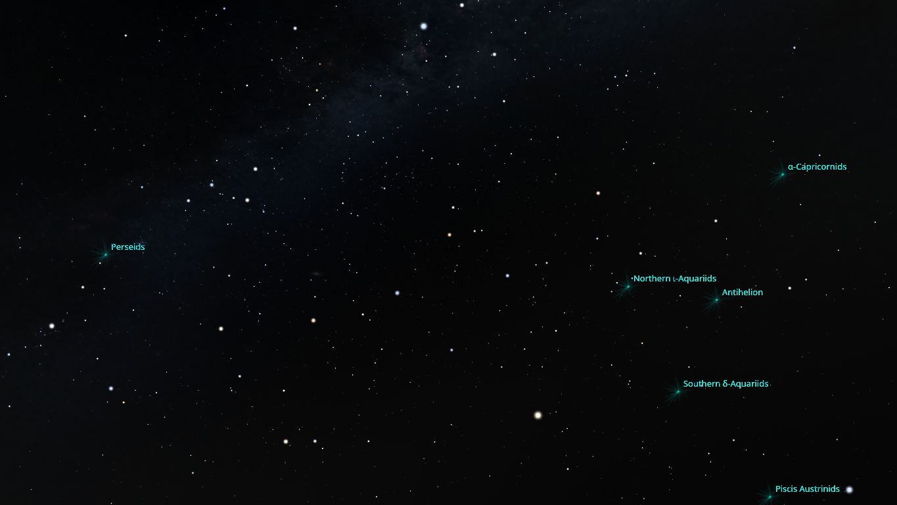
src/digital_twin/test_images/testing50.png
