IvaylooTs/StarTracker/src/digital_twin/test_images/testing51.png

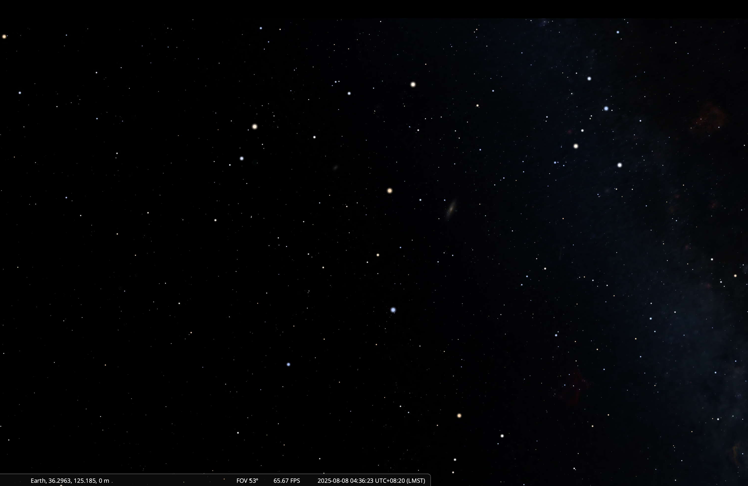
src/digital_twin/test_images/testing51.png
