IvaylooTs/StarTracker/src/digital_twin/test_images/testing53.png

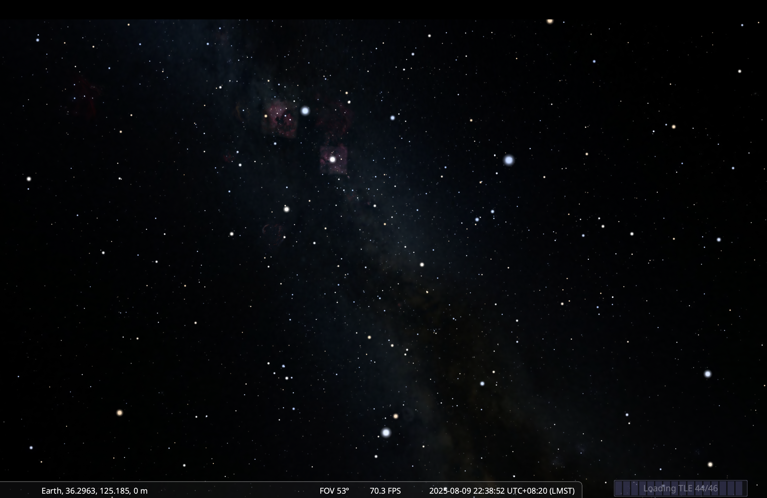
src/digital_twin/test_images/testing53.png
