IvaylooTs/StarTracker/src/digital_twin/test_images/testing54.png

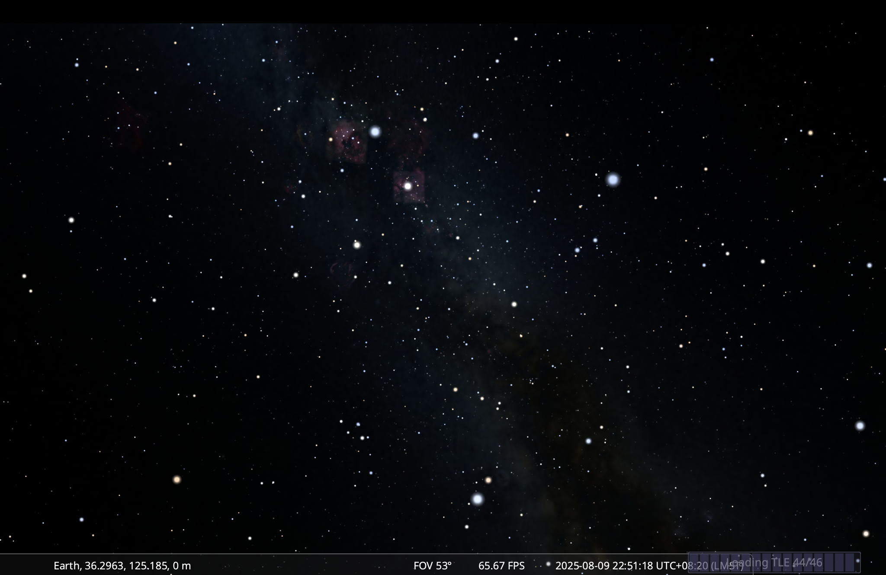
src/digital_twin/test_images/testing54.png
