IvaylooTs/StarTracker/src/digital_twin/test_images/testing61.png

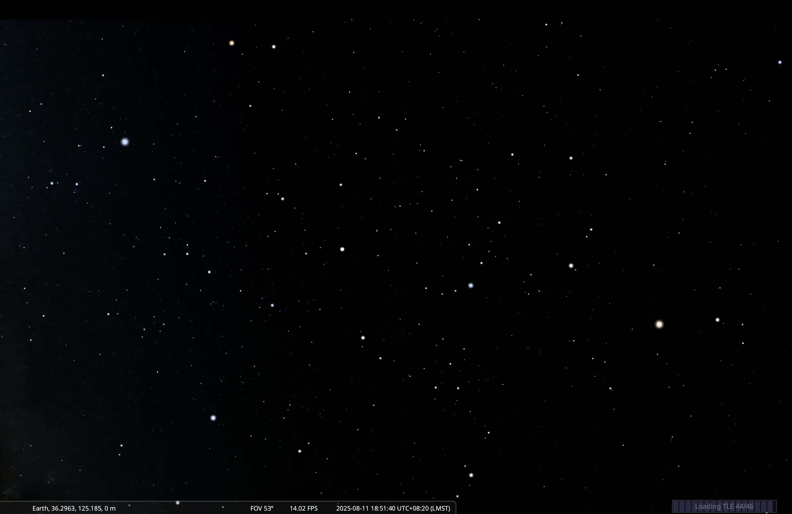
src/digital_twin/test_images/testing61.png
