IvaylooTs/StarTracker/src/digital_twin/test_images/testing63.png

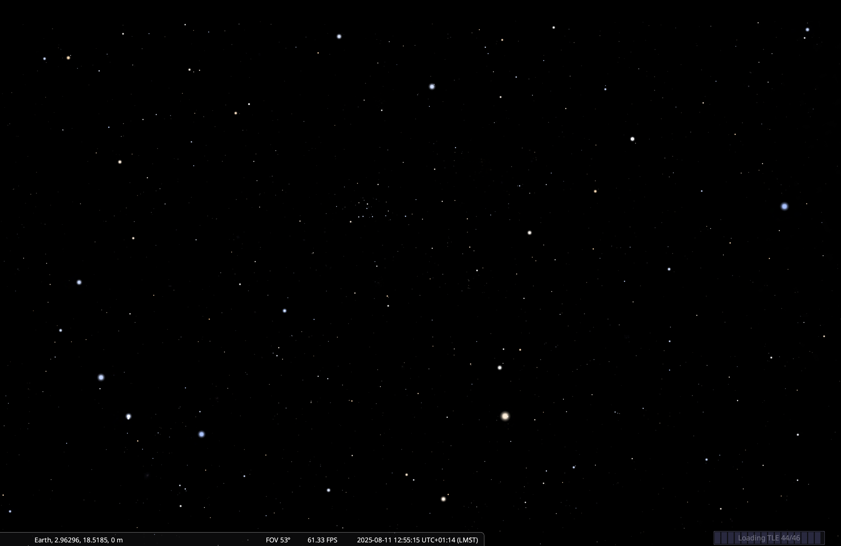
src/digital_twin/test_images/testing63.png
