IvaylooTs/StarTracker/src/digital_twin/test_images/testing65.png

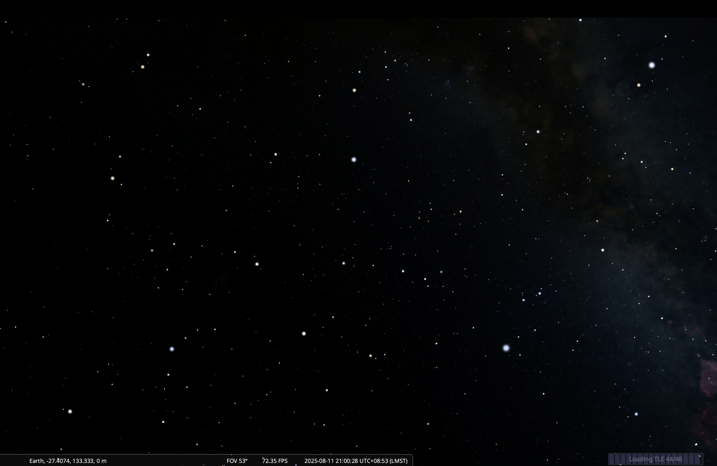
src/digital_twin/test_images/testing65.png
