IvaylooTs/StarTracker/src/digital_twin/test_images/testing66.png

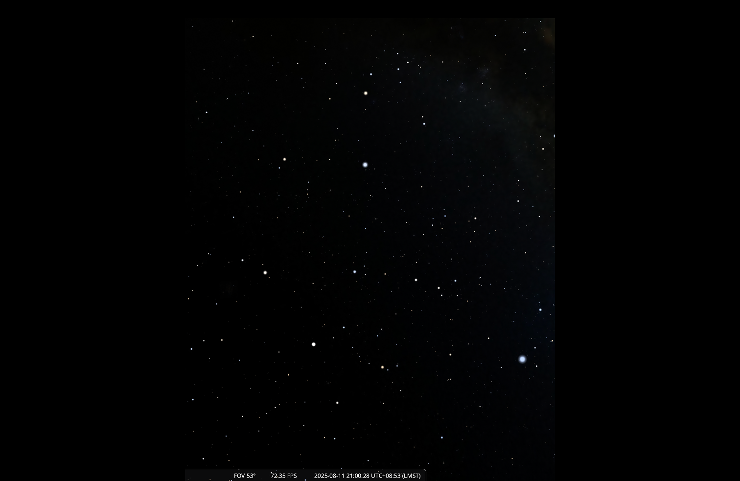
src/digital_twin/test_images/testing66.png
