IvaylooTs/StarTracker/src/digital_twin/test_images/testing67.png

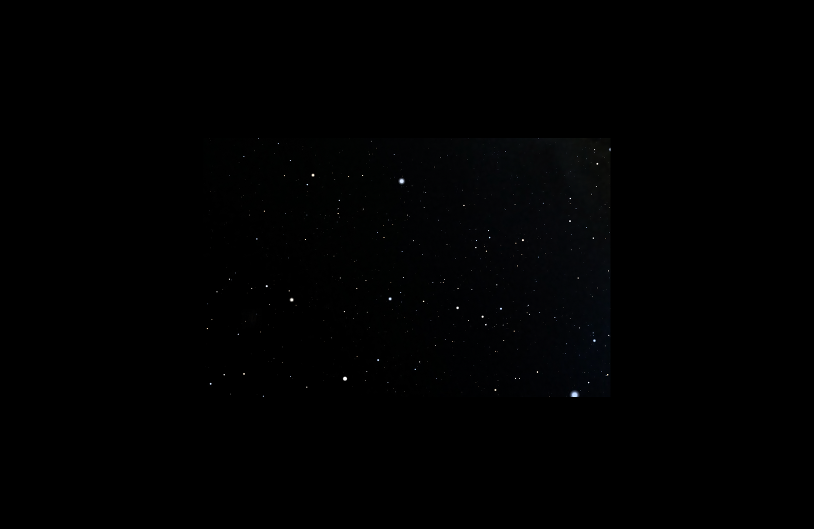
src/digital_twin/test_images/testing67.png
