IvaylooTs/StarTracker/src/digital_twin/test_images/testing68.png

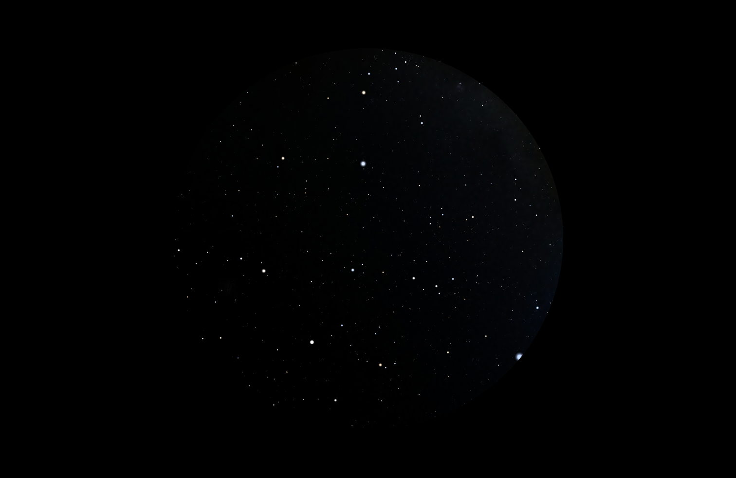
src/digital_twin/test_images/testing68.png
