IvaylooTs/StarTracker/src/digital_twin/test_images/testing69.png

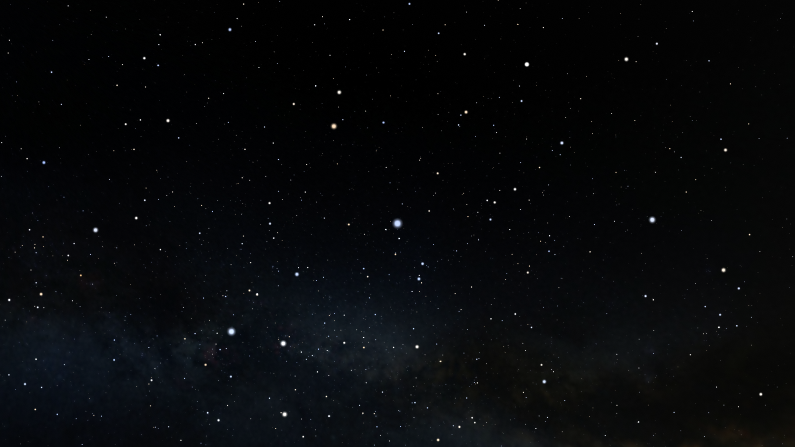
src/digital_twin/test_images/testing69.png
