IvaylooTs/StarTracker/src/digital_twin/test_images/testing70.png

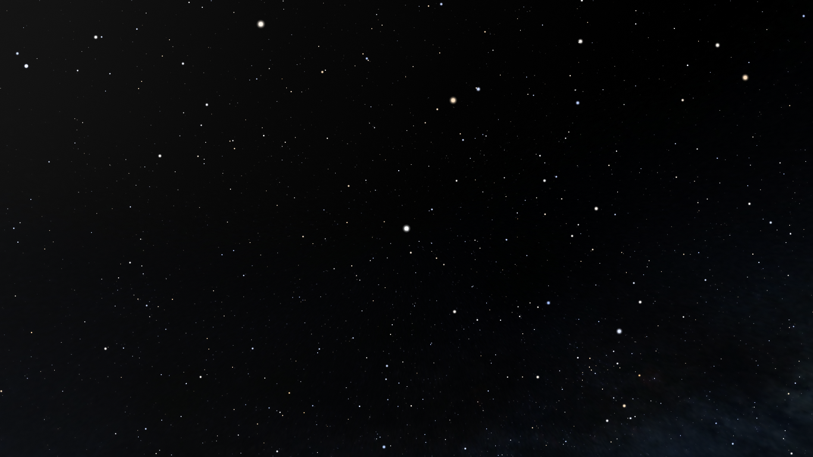
src/digital_twin/test_images/testing70.png
