IvaylooTs/StarTracker/src/digital_twin/test_images/testing71.png

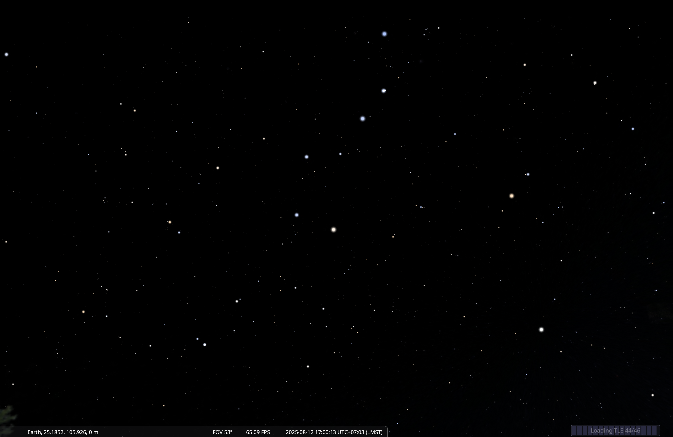
src/digital_twin/test_images/testing71.png
