IvaylooTs/StarTracker/src/digital_twin/test_images/testing72.png

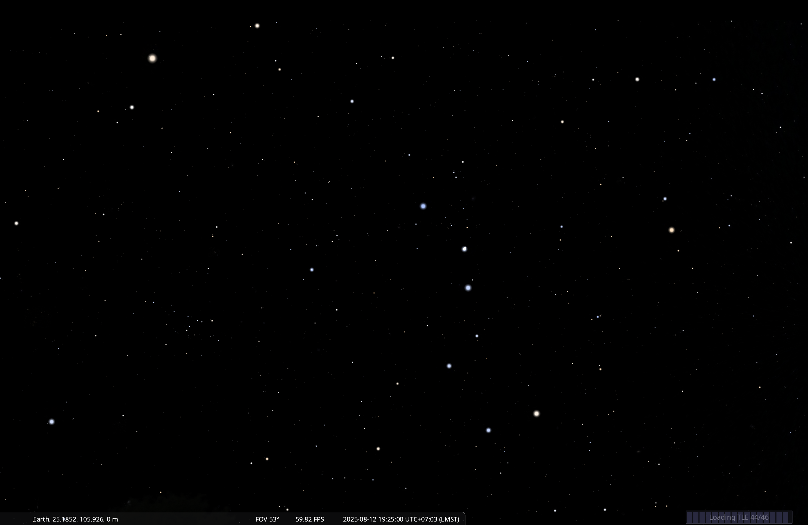
src/digital_twin/test_images/testing72.png
