IvaylooTs/StarTracker/src/digital_twin/test_images/testing73.png

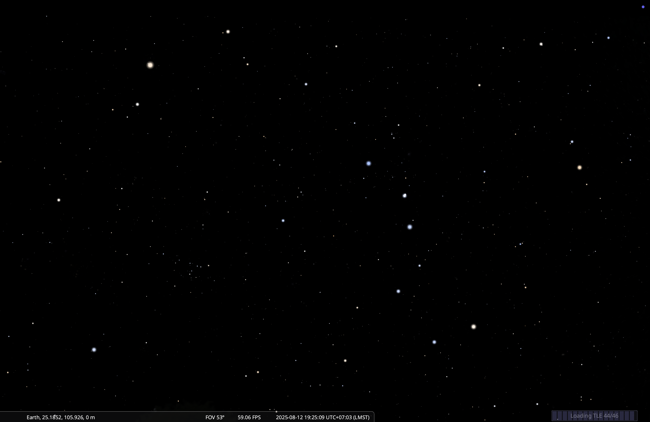
src/digital_twin/test_images/testing73.png
