IvaylooTs/StarTracker/src/digital_twin/test_images/testing74.png

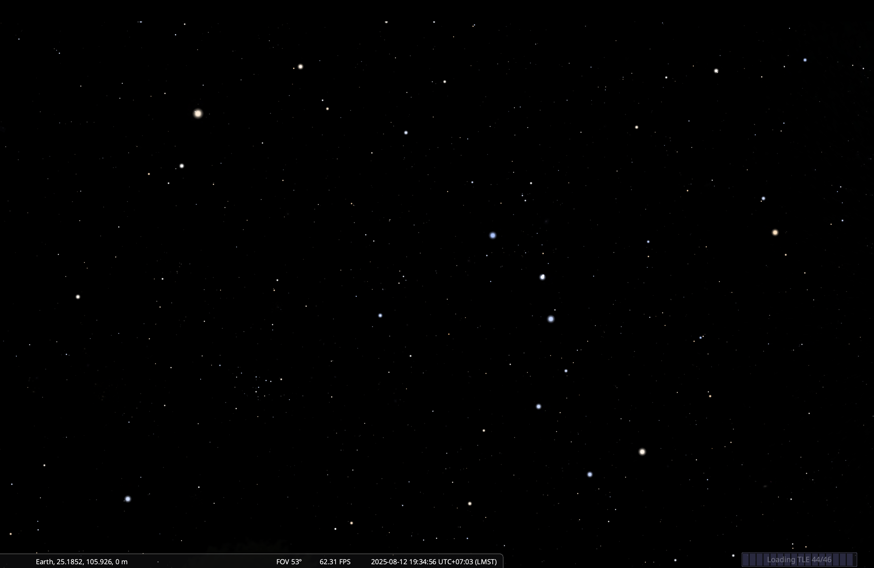
src/digital_twin/test_images/testing74.png
