IvaylooTs/StarTracker/src/digital_twin/test_images/testing75.png

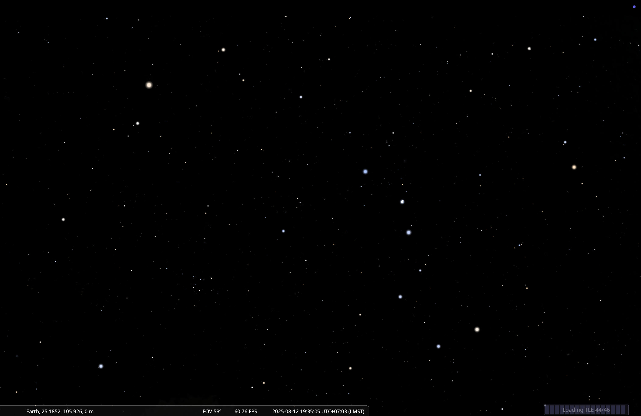
src/digital_twin/test_images/testing75.png
