IvaylooTs/StarTracker/src/digital_twin/test_images/testing76.png

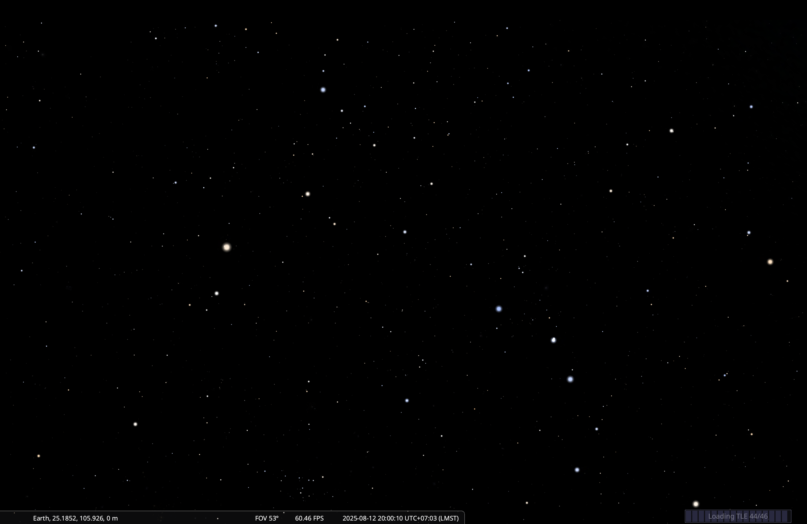
src/digital_twin/test_images/testing76.png
