IvaylooTs/StarTracker/src/digital_twin/test_images/testing78.png

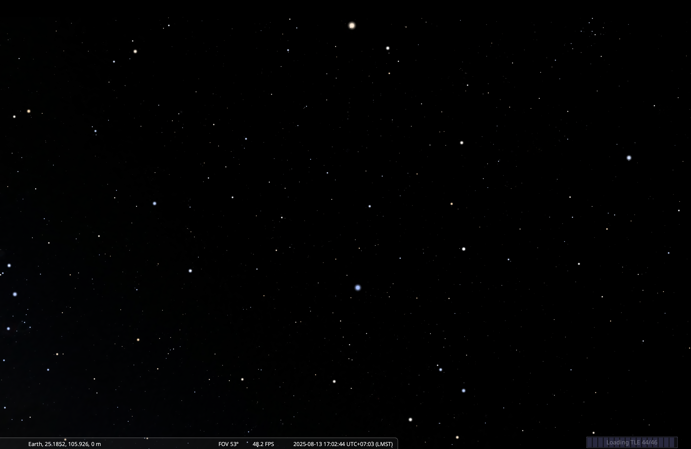
src/digital_twin/test_images/testing78.png
