IvaylooTs/StarTracker/src/digital_twin/test_images/testing80.png

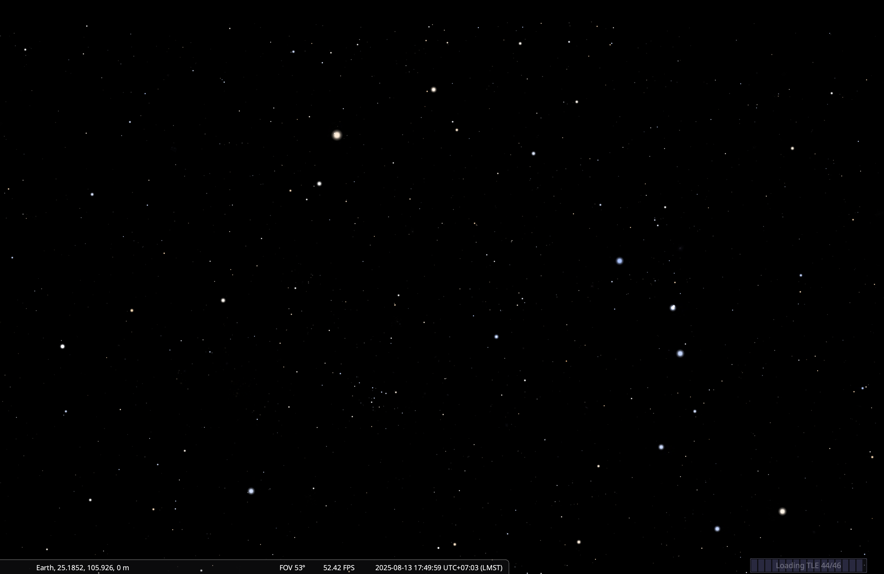
src/digital_twin/test_images/testing80.png
