IvaylooTs/StarTracker/src/digital_twin/test_images/testing81.png

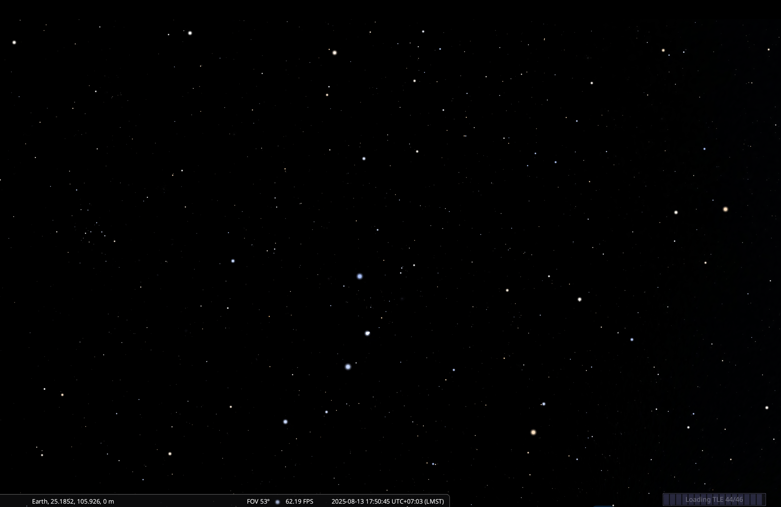
src/digital_twin/test_images/testing81.png
