IvaylooTs/StarTracker/src/digital_twin/test_images/testing82.png

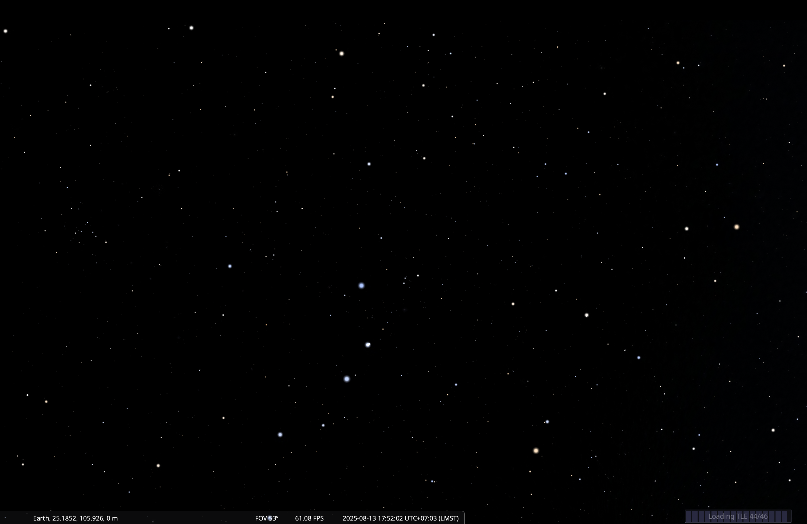
src/digital_twin/test_images/testing82.png
