IvaylooTs/StarTracker/src/digital_twin/test_images/testing83.png

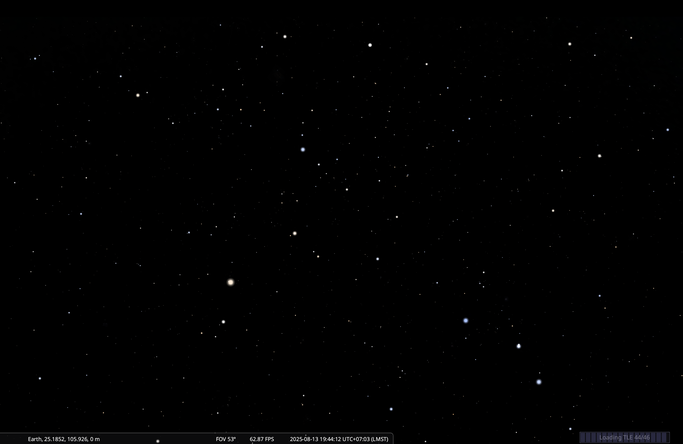
src/digital_twin/test_images/testing83.png
