IvaylooTs/StarTracker/src/digital_twin/test_images/testing84.png

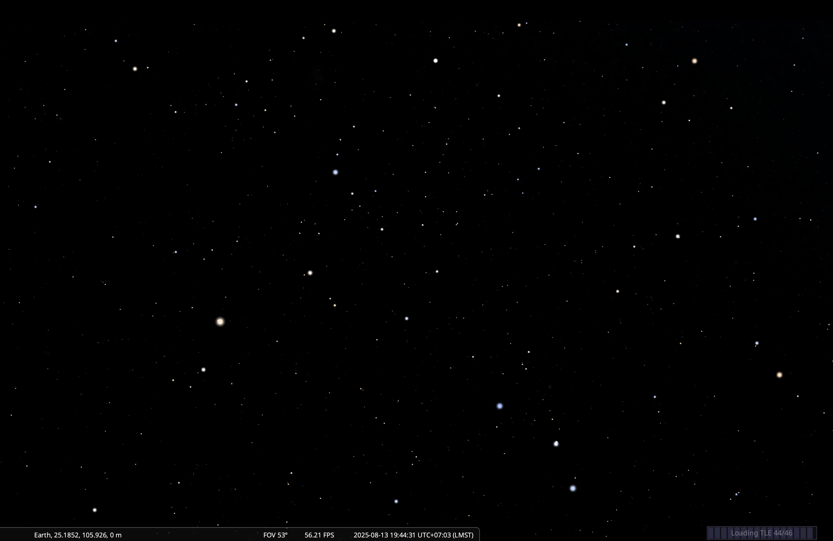
src/digital_twin/test_images/testing84.png
