IvaylooTs/StarTracker/src/digital_twin/test_images/testing85.png

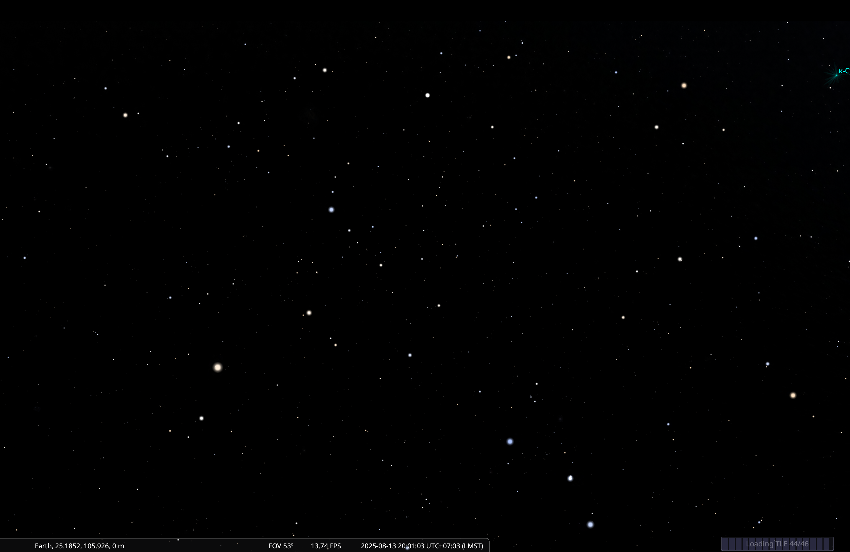
src/digital_twin/test_images/testing85.png
