IvaylooTs/StarTracker/src/digital_twin/test_images/testing86.png

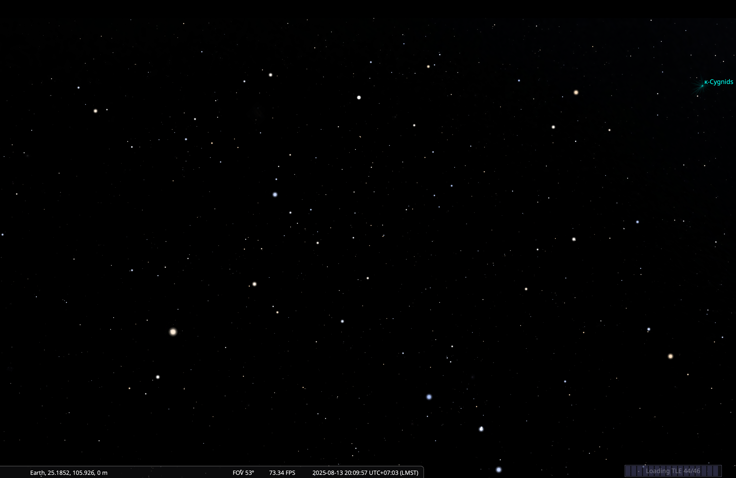
src/digital_twin/test_images/testing86.png
