IvaylooTs/StarTracker/src/digital_twin/test_images/testing89.png

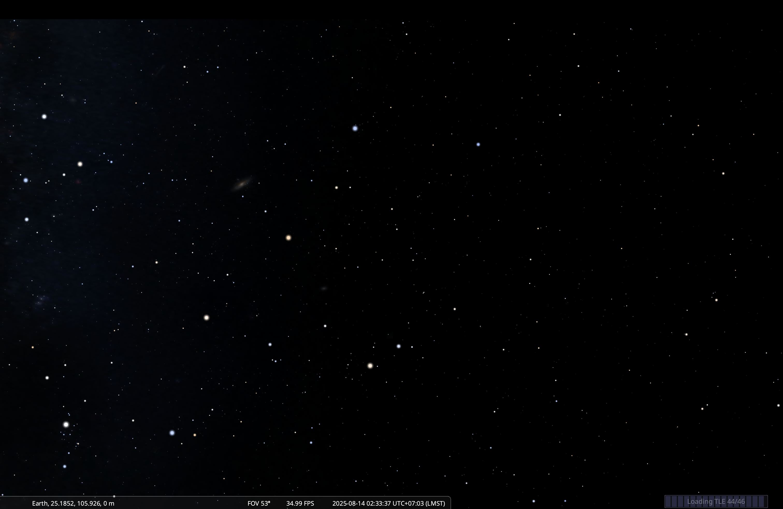
src/digital_twin/test_images/testing89.png
