IvaylooTs/StarTracker/src/digital_twin/test_images/testing91.png

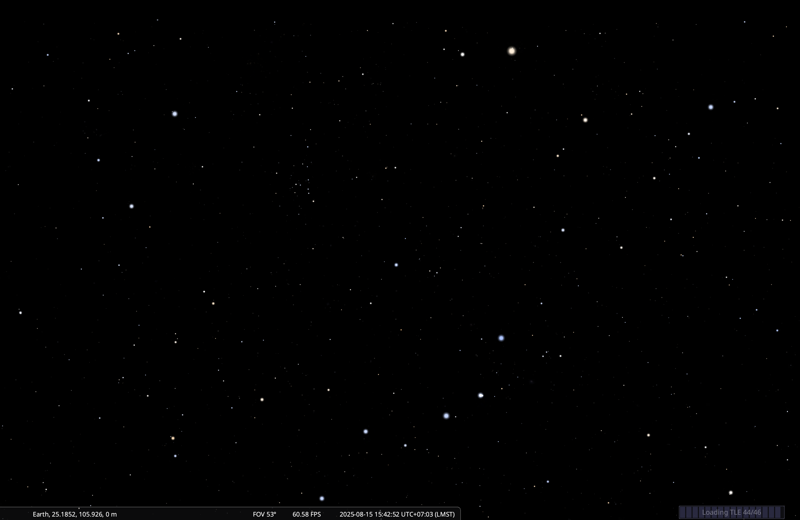
src/digital_twin/test_images/testing91.png
