IvaylooTs/StarTracker/src/digital_twin/test_images/testing92.png

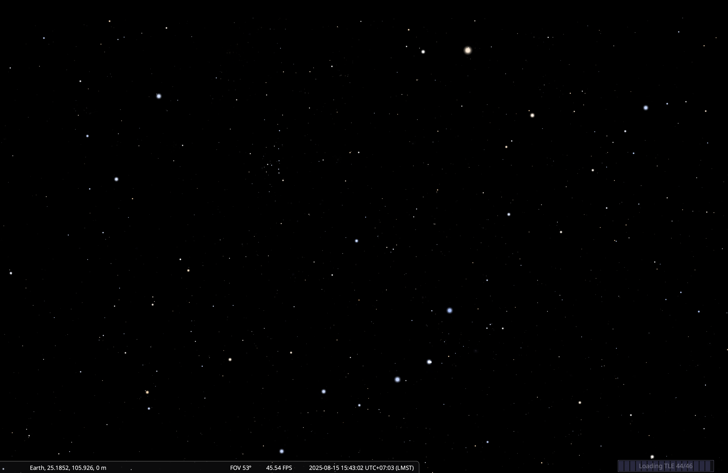
src/digital_twin/test_images/testing92.png
