IvaylooTs/StarTracker/src/digital_twin/test_images/testing93.png

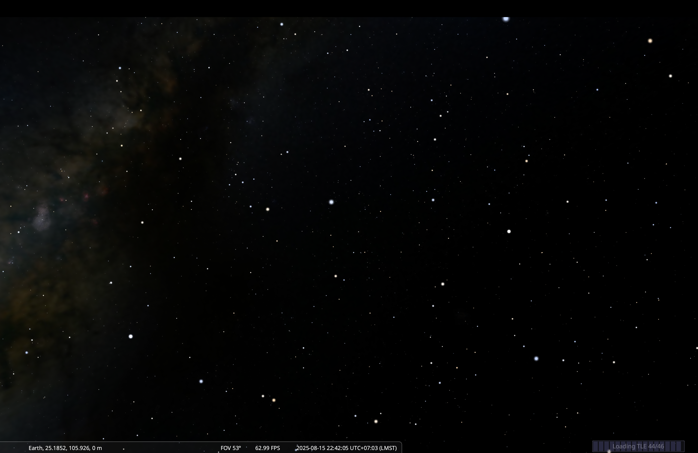
src/digital_twin/test_images/testing93.png
