IvaylooTs/StarTracker/src/digital_twin/test_images/testing95.png

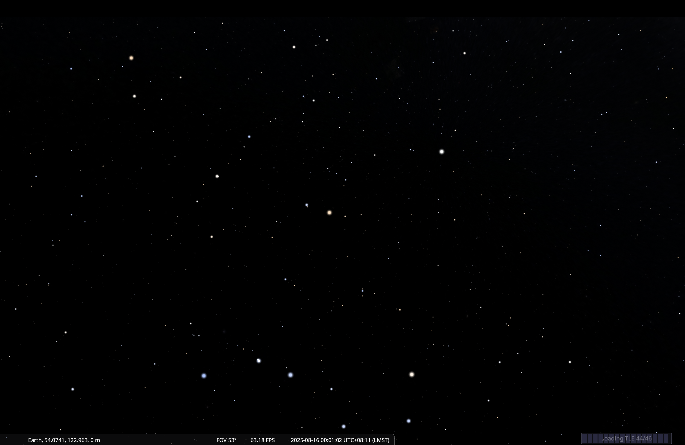
src/digital_twin/test_images/testing95.png
