IvaylooTs/StarTracker/src/digital_twin/test_images/testing96.png

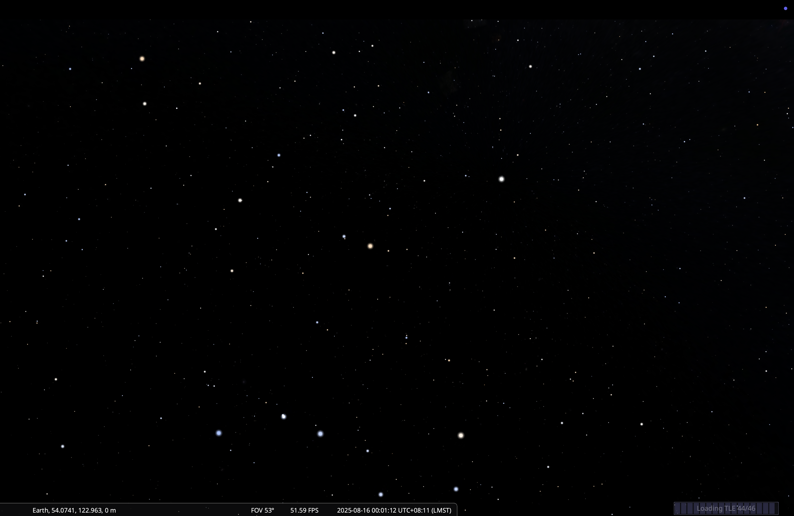
src/digital_twin/test_images/testing96.png
