IvaylooTs/StarTracker/src/digital_twin/test_images/testing99.png

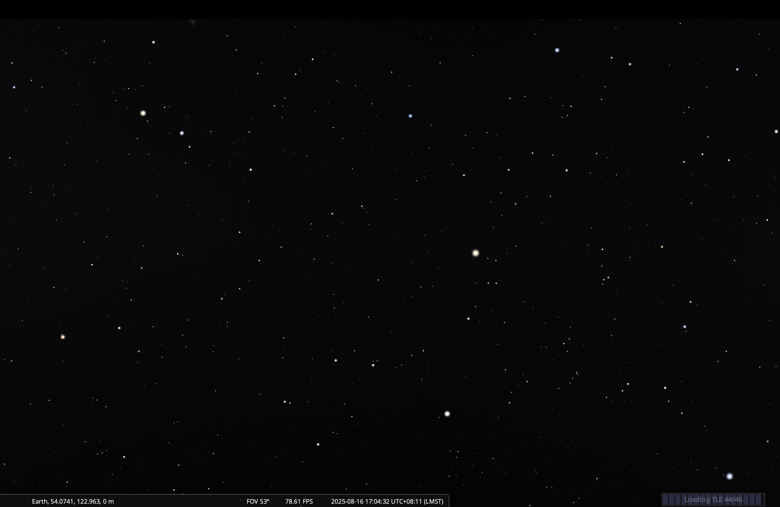
src/digital_twin/test_images/testing99.png
