IvaylooTs/StarTracker/src/digital_twin/test_images/testing100.png

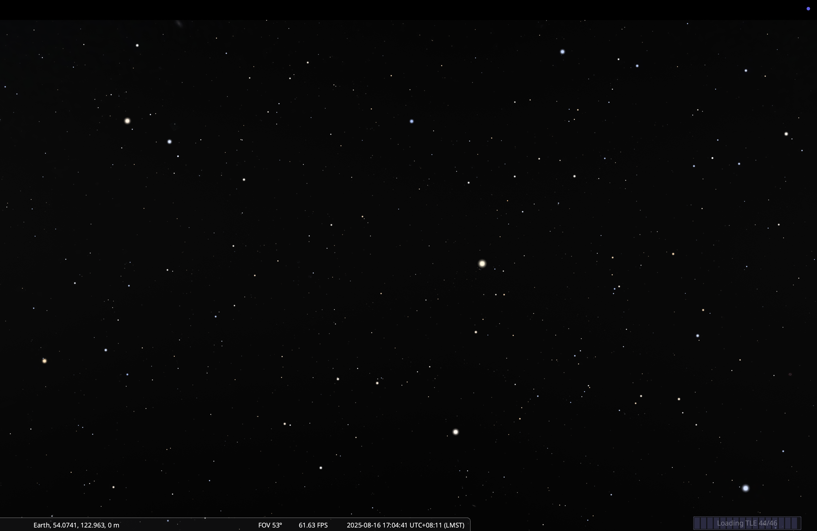
src/digital_twin/test_images/testing100.png
