IvaylooTs/StarTracker/src/digital_twin/test_images/testing101.png

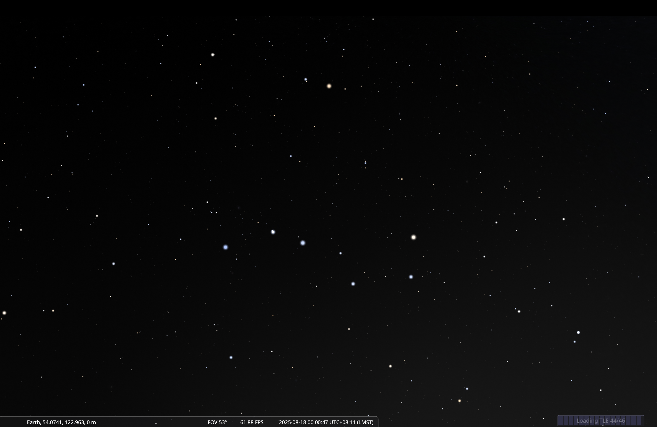
src/digital_twin/test_images/testing101.png
