IvaylooTs/StarTracker/src/digital_twin/test_images/testing102.png

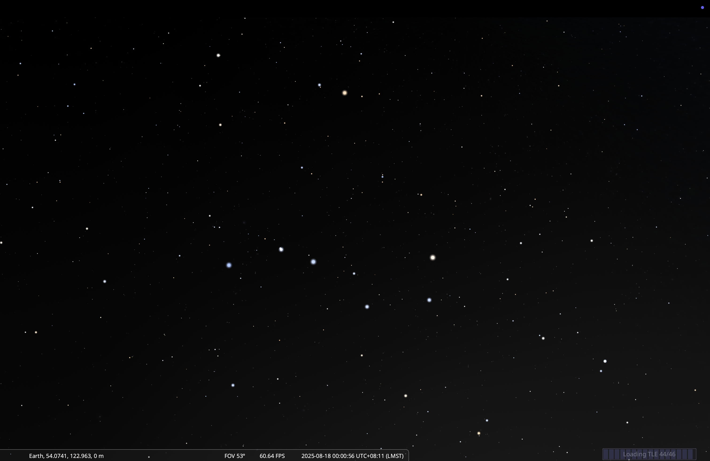
src/digital_twin/test_images/testing102.png
