IvaylooTs/StarTracker/src/digital_twin/test_images/testing104.png

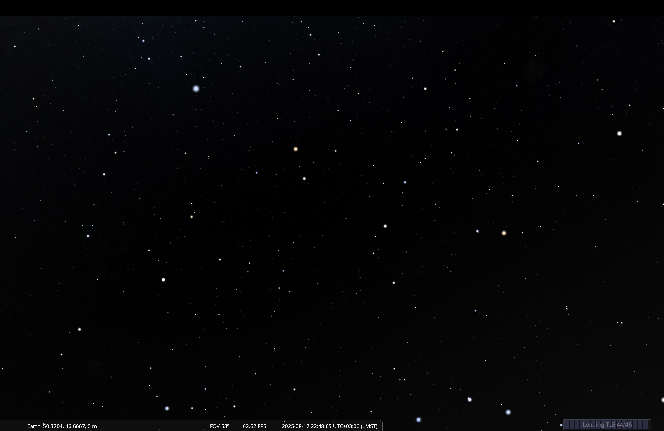
src/digital_twin/test_images/testing104.png
