IvaylooTs/StarTracker/src/digital_twin/test_images/testing110.png

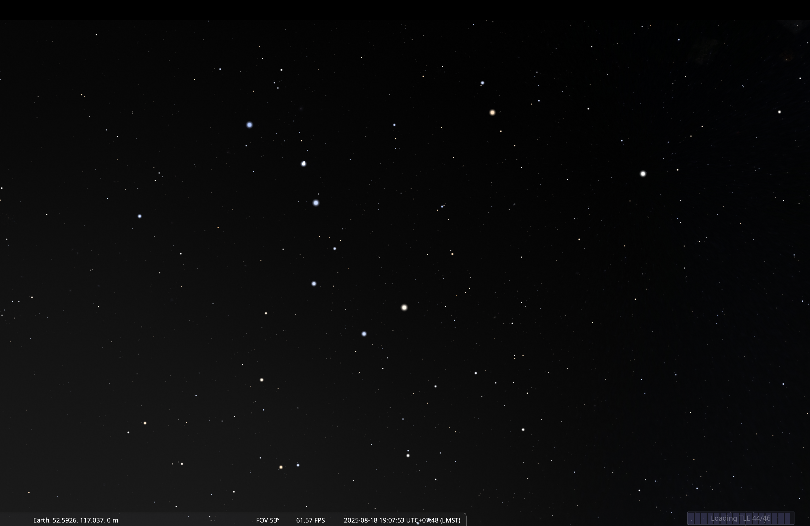
src/digital_twin/test_images/testing110.png
