IvaylooTs/StarTracker/src/digital_twin/test_images/testing112.png

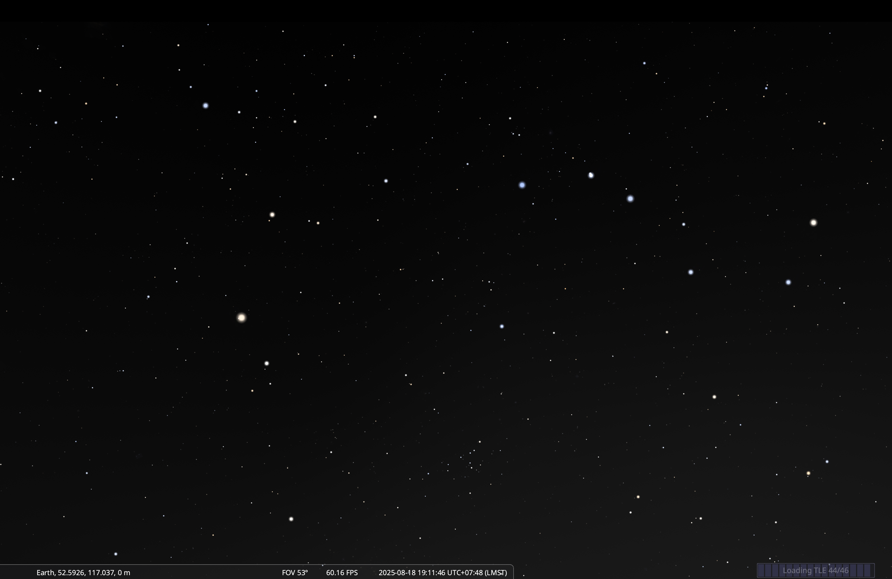
src/digital_twin/test_images/testing112.png
