IvaylooTs/StarTracker/src/digital_twin/test_images/testing113.png

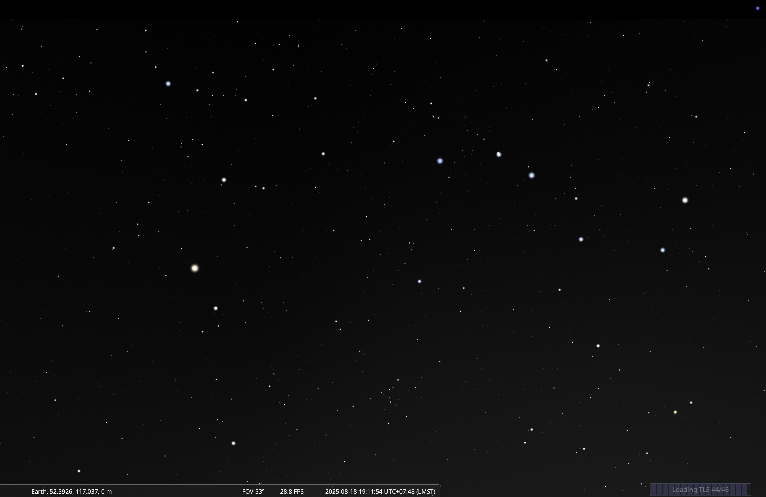
src/digital_twin/test_images/testing113.png
