IvaylooTs/StarTracker/src/digital_twin/test_images/testing114.png

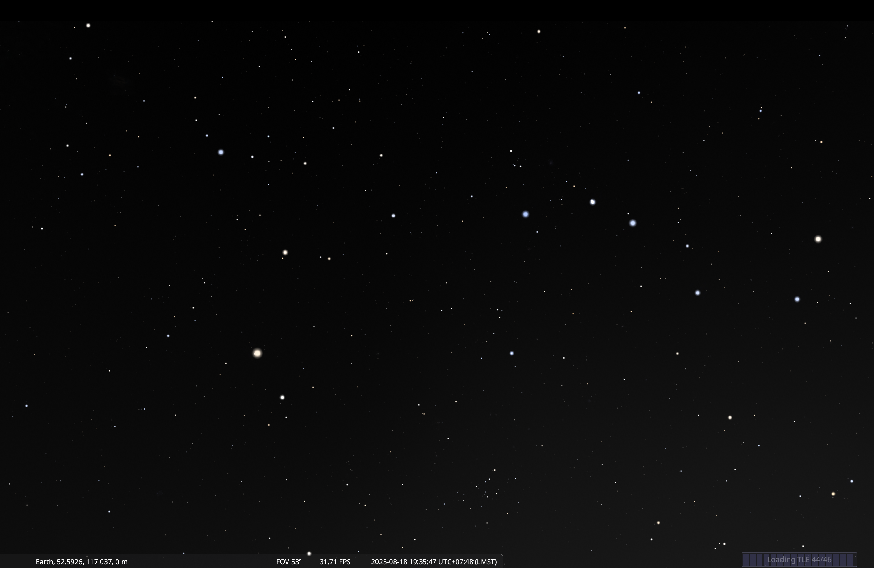
src/digital_twin/test_images/testing114.png
