IvaylooTs/StarTracker/src/digital_twin/test_images/testing115.png

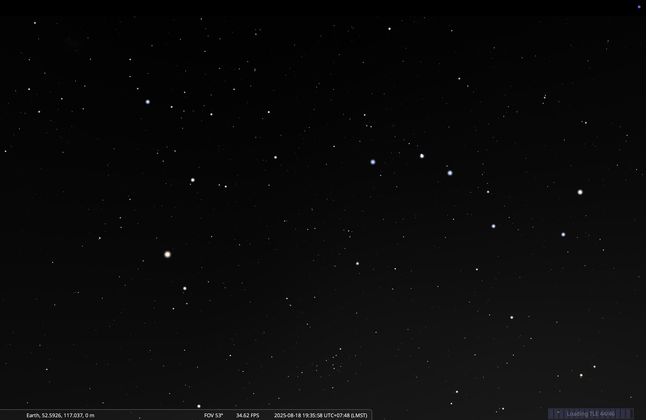
src/digital_twin/test_images/testing115.png
