IvaylooTs/StarTracker/src/digital_twin/test_images/testing116.png

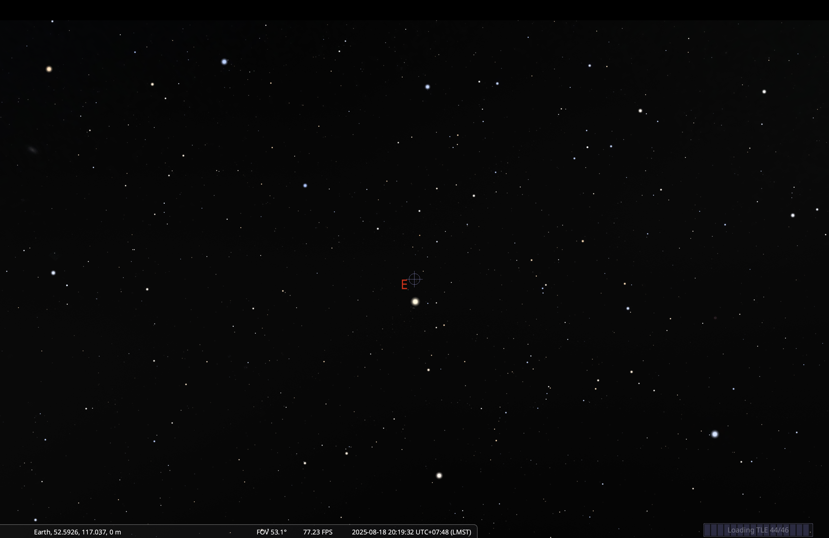
src/digital_twin/test_images/testing116.png
