IvaylooTs/StarTracker/src/digital_twin/test_images/testing117.png

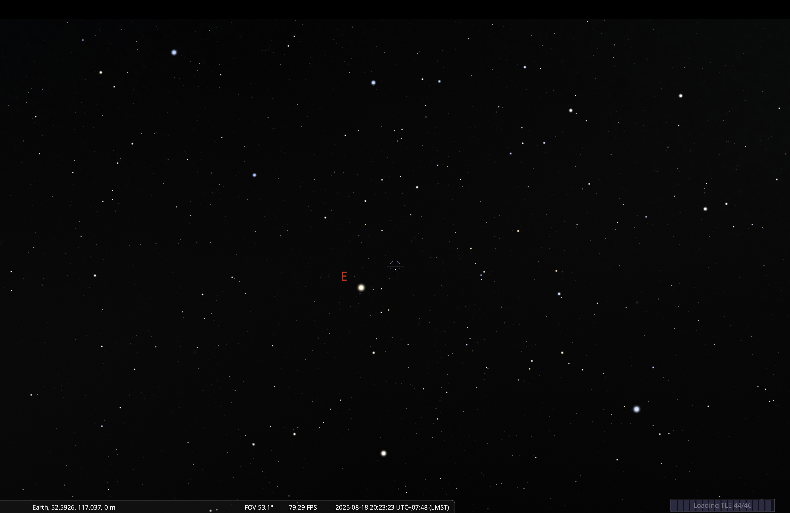
src/digital_twin/test_images/testing117.png
