IvaylooTs/StarTracker/src/digital_twin/test_images/testing118.png

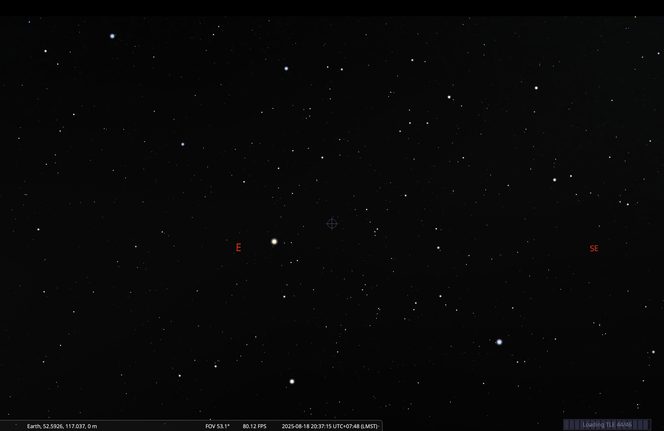
src/digital_twin/test_images/testing118.png
