IvaylooTs/StarTracker/src/digital_twin/test_images/testing142.png

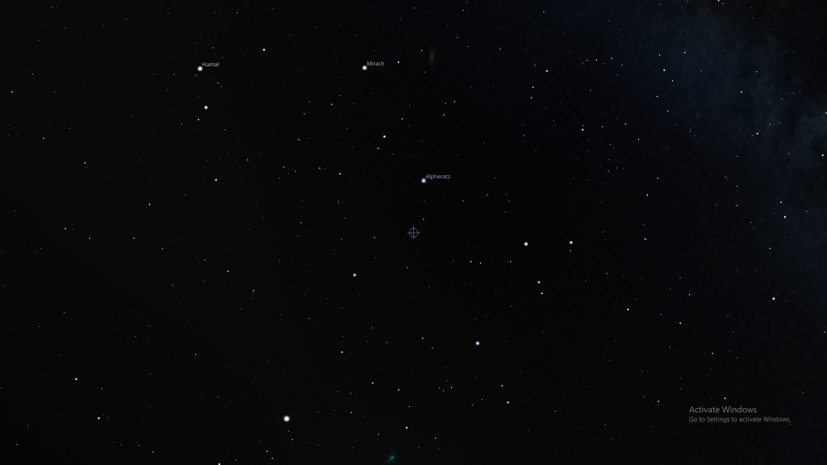
src/digital_twin/test_images/testing142.png
