IvaylooTs/StarTracker/src/digital_twin/test_images/testing.png

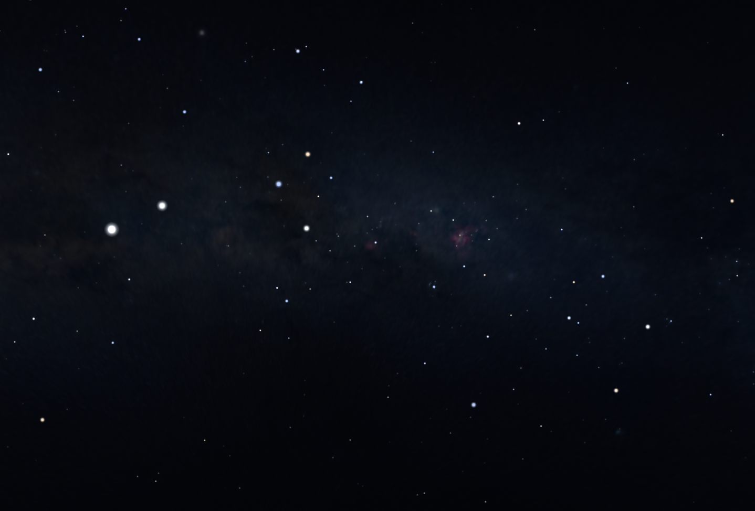
src/digital_twin/test_images/testing.png
