IvaylooTs/StarTracker/src/digital_twin/test_images/vertical_000_deg001.png

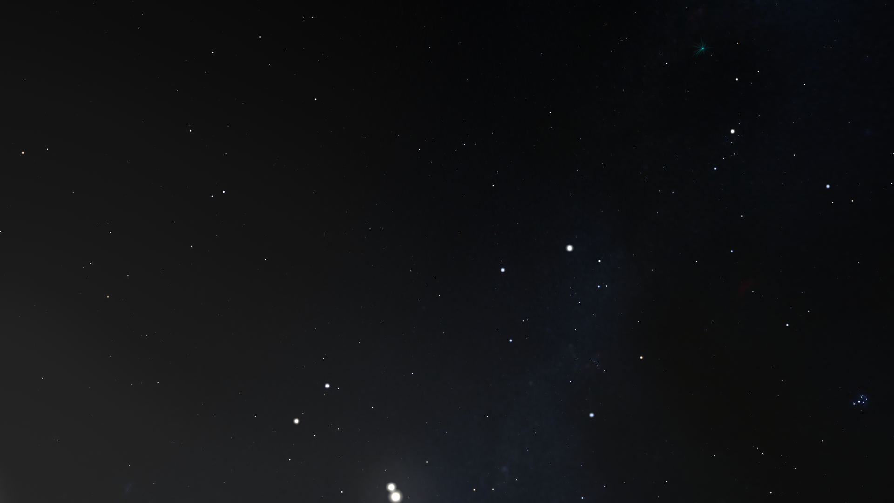
src/digital_twin/test_images/vertical_000_deg001.png
