IvaylooTs/StarTracker/src/digital_twin/test_images/vertical_090_deg001.png

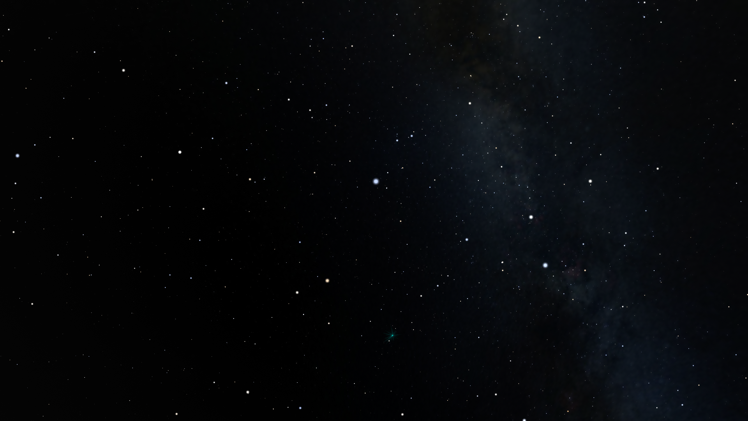
src/digital_twin/test_images/vertical_090_deg001.png
