IvaylooTs/StarTracker/src/star_tracking/tests/test_images/testing1.png

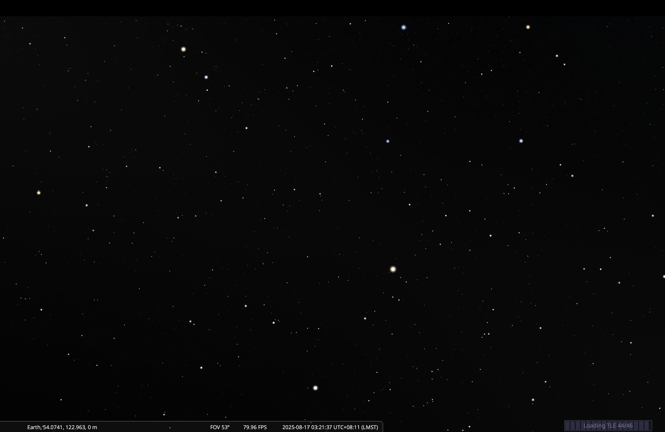
src/star_tracking/tests/test_images/testing1.png
