IvaylooTs/StarTracker/src/test/stars_identified.png

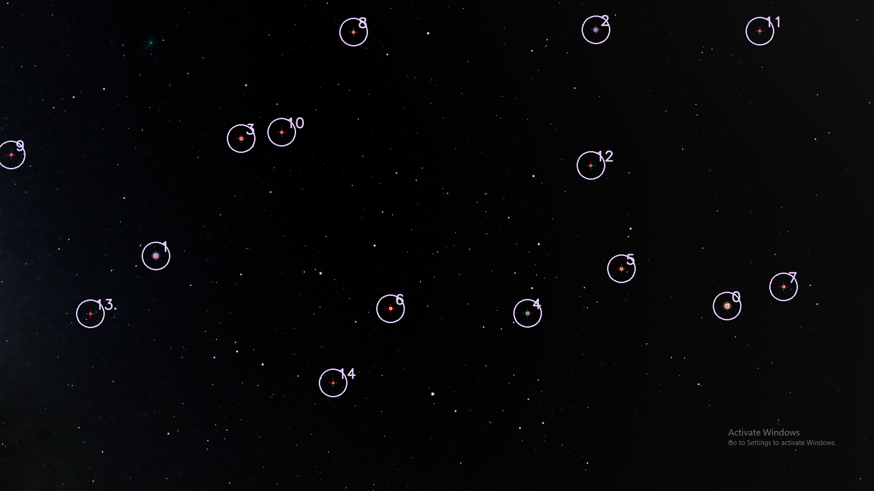
src/test/stars_identified.png
