IvaylooTs/StarTracker/Testing/Images/didntwork2.jpg

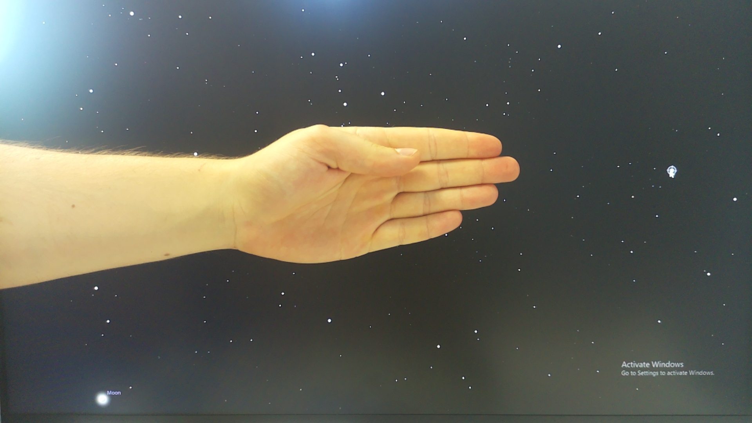
Testing/Images/didntwork2.jpg
