IvaylooTs/StarTracker/Testing/Images/didntwork.jpg

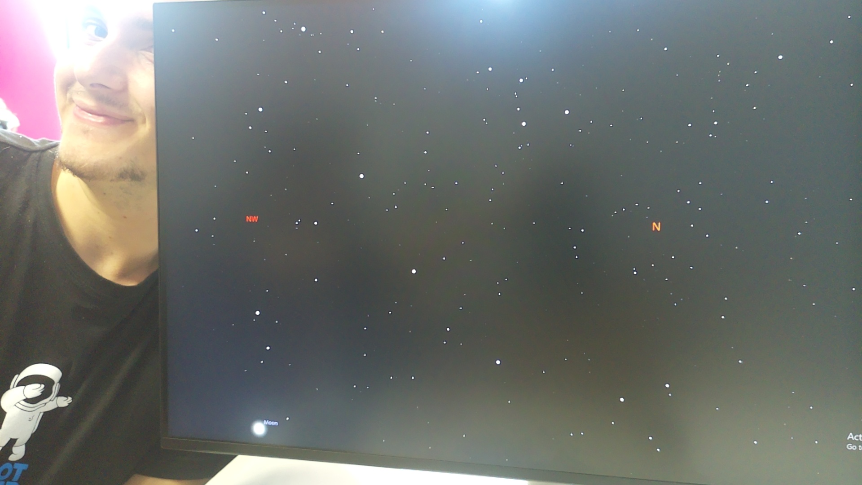
Testing/Images/didntwork.jpg
