IvaylooTs/StarTracker/Testing/Images/didnwork.jpg

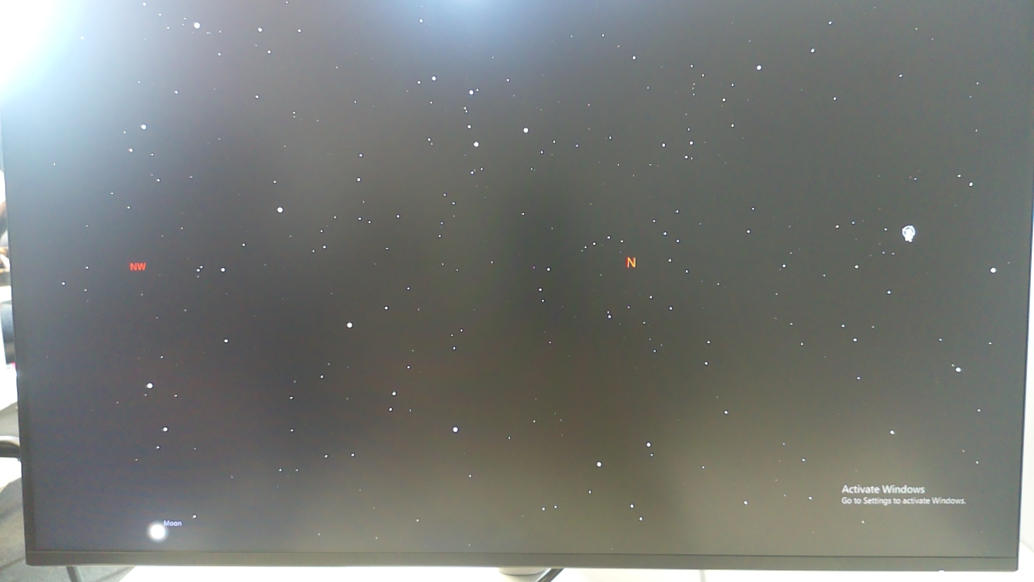
Testing/Images/didnwork.jpg
