IvaylooTs/StarTracker/Testing/Images/ErrorDetermination.jpg

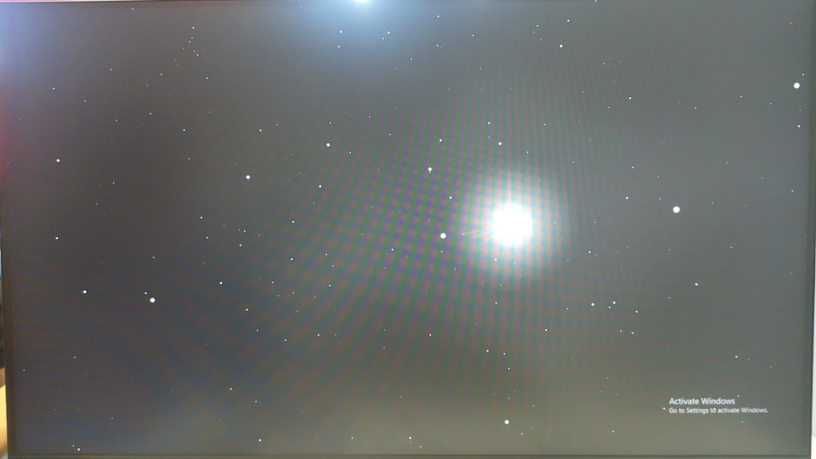
Testing/Images/ErrorDetermination.jpg
