IvaylooTs/StarTracker/Testing/Images/mouseError.jpg

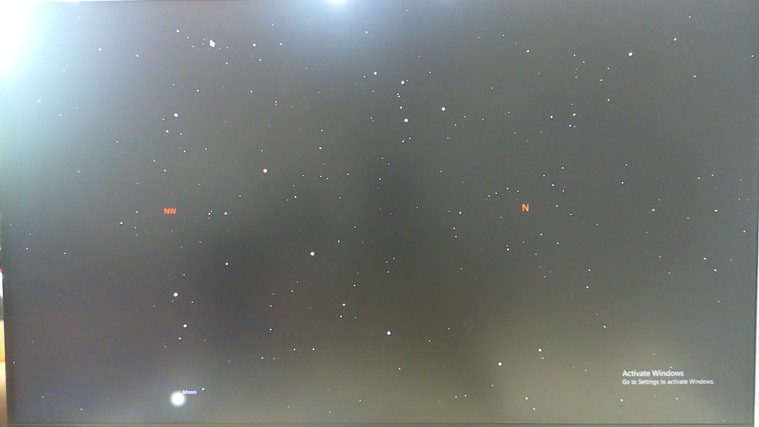
Testing/Images/mouseError.jpg
