IvaylooTs/StarTracker/Testing/Images/photo_20250814_163915.jpg

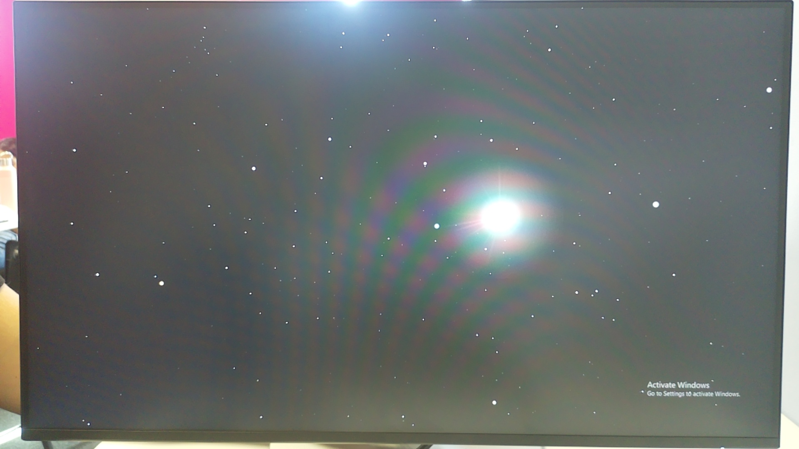
Testing/Images/photo_20250814_163915.jpg
