IvaylooTs/StarTracker/Testing/Images/photo_20250814_164120.jpg

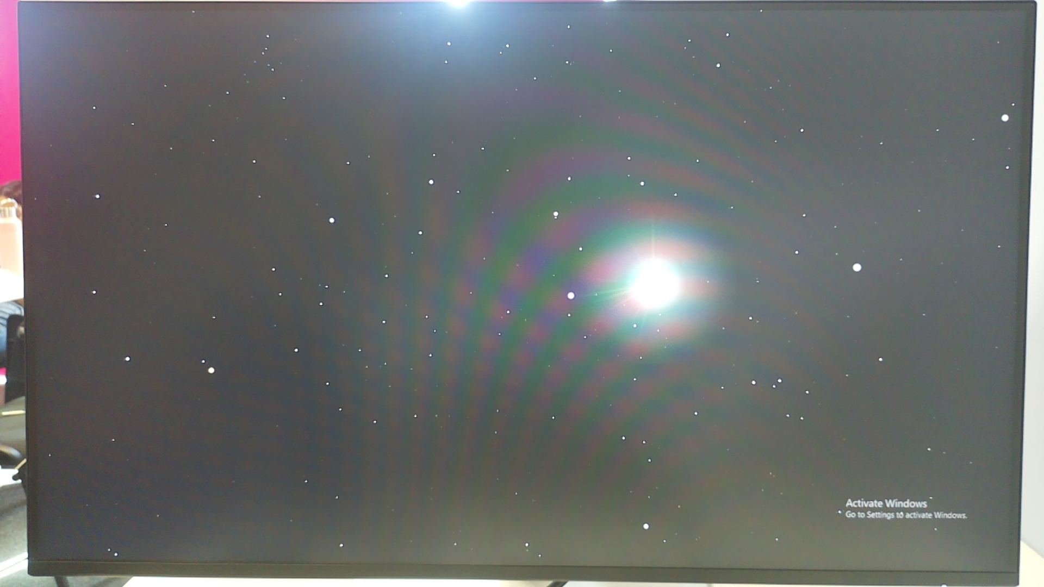
Testing/Images/photo_20250814_164120.jpg
