IvaylooTs/StarTracker/Testing/Images/photo_20250814_164353.jpg

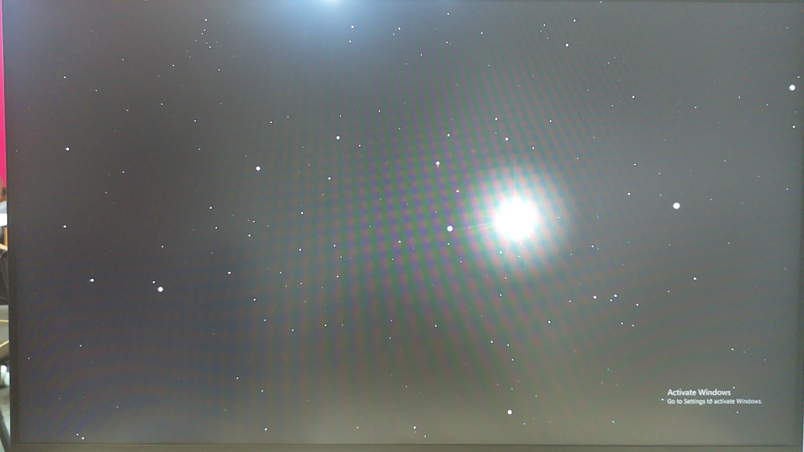
Testing/Images/photo_20250814_164353.jpg
