IvaylooTs/StarTracker/Testing/Images/photo_20250814_164610.jpg

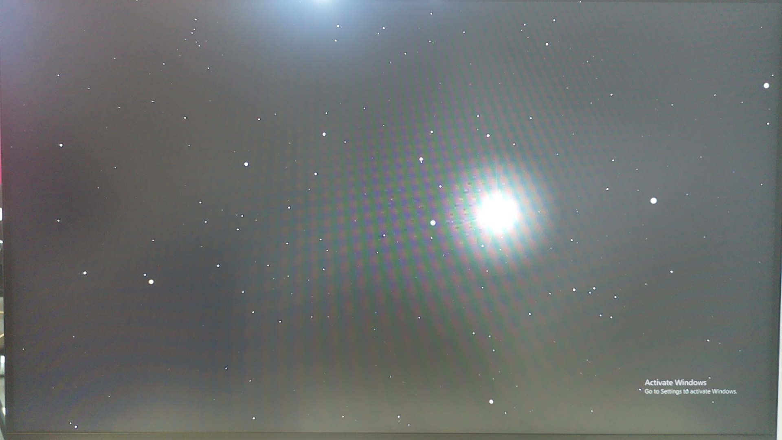
Testing/Images/photo_20250814_164610.jpg
