IvaylooTs/StarTracker/Testing/Images/photo_20250814_165400.jpg

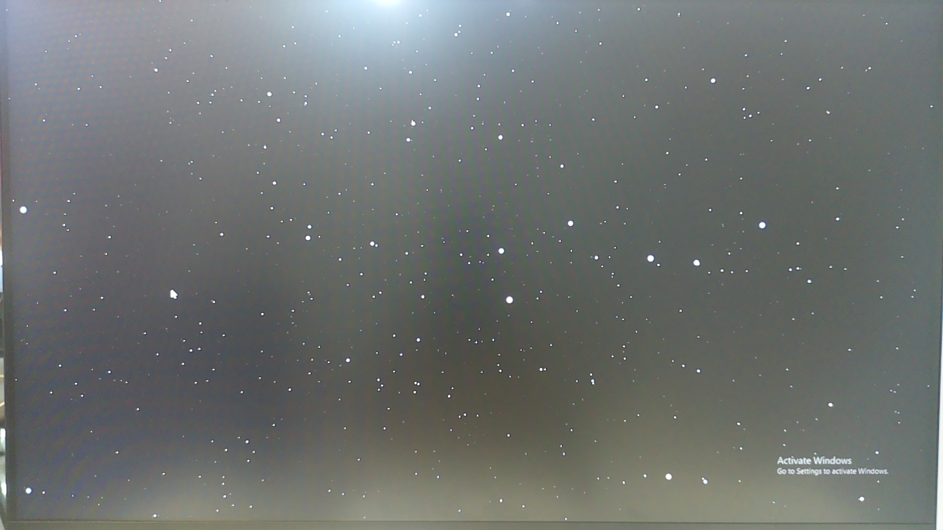
Testing/Images/photo_20250814_165400.jpg
