IvaylooTs/StarTracker/Testing/Images/photo_20250814_165807.jpg

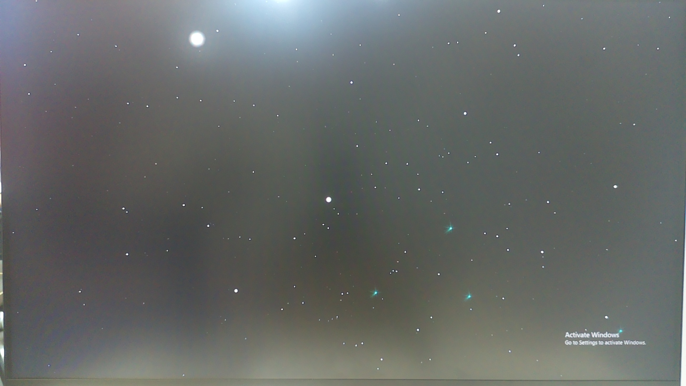
Testing/Images/photo_20250814_165807.jpg
