IvaylooTs/StarTracker/Testing/Images/photo_20250814_170111.jpg

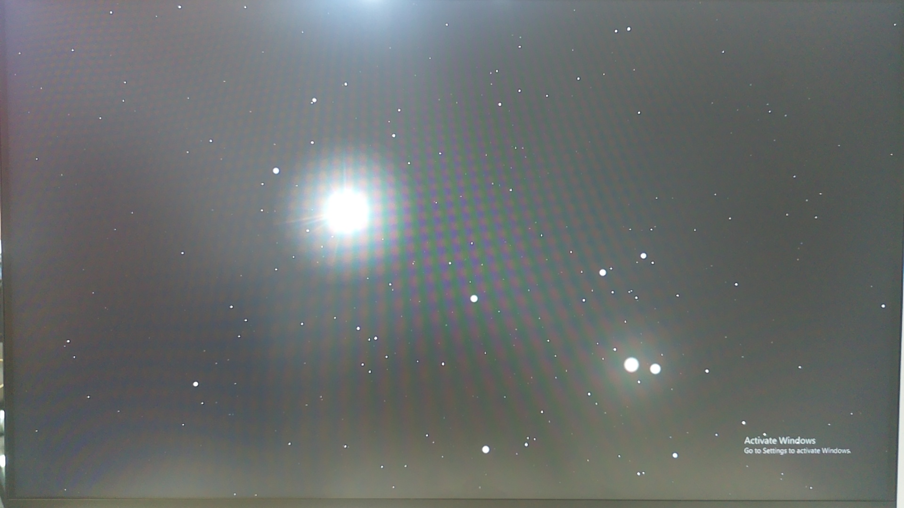
Testing/Images/photo_20250814_170111.jpg
