IvaylooTs/StarTracker/Testing/Images/photo_20250814_170401.jpg

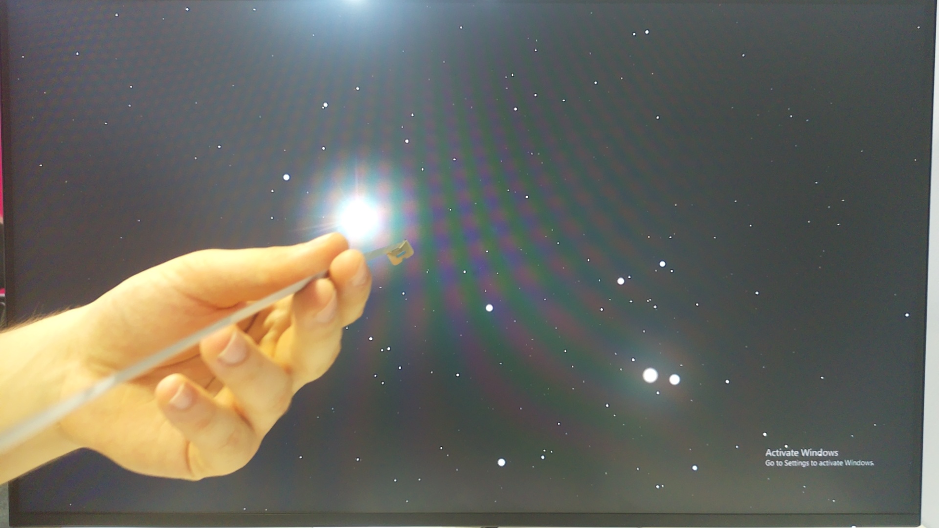
Testing/Images/photo_20250814_170401.jpg
