IvaylooTs/StarTracker/Testing/Images/photo_20250814_170949.jpg

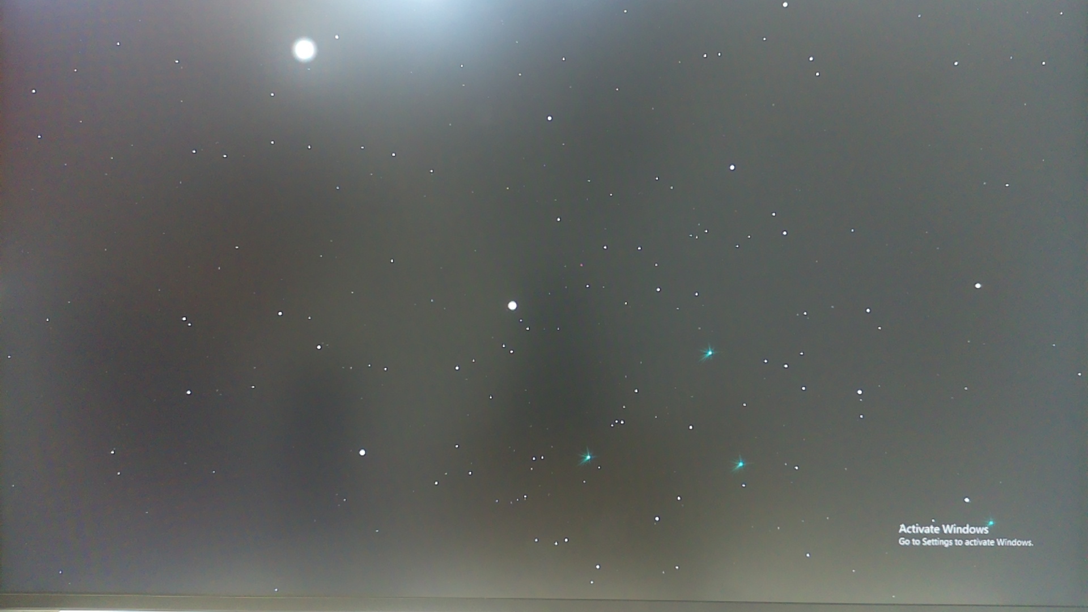
Testing/Images/photo_20250814_170949.jpg
