IvaylooTs/StarTracker/Testing/Images/photo_20250814_171018.jpg

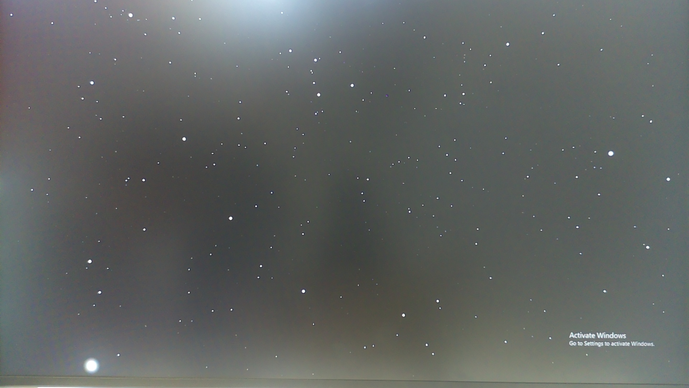
Testing/Images/photo_20250814_171018.jpg
