IvaylooTs/StarTracker/Testing/Images/photo_20250814_171108.jpg

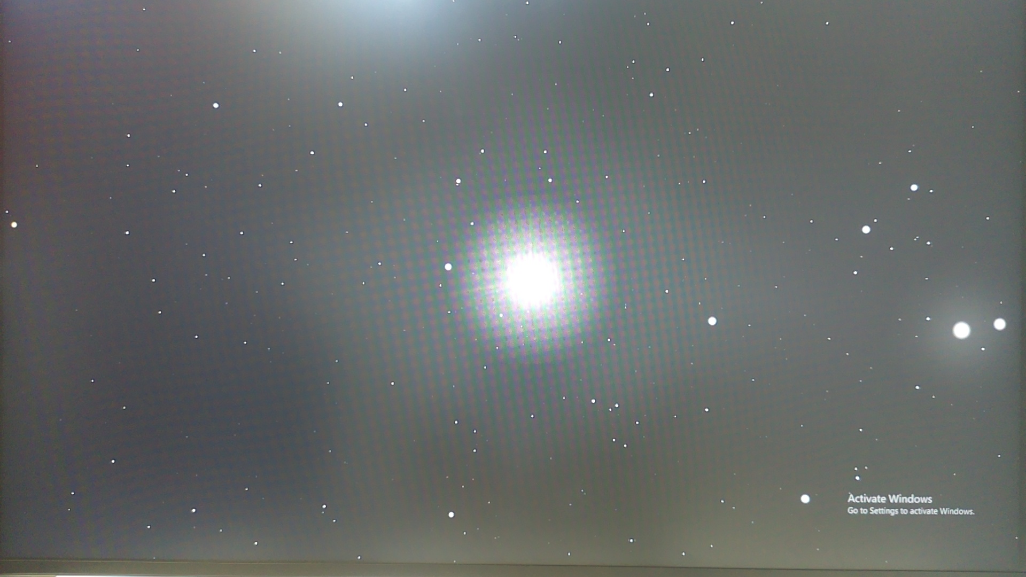
Testing/Images/photo_20250814_171108.jpg
