IvaylooTs/StarTracker/Testing/Images/photo_20250814_171217.jpg

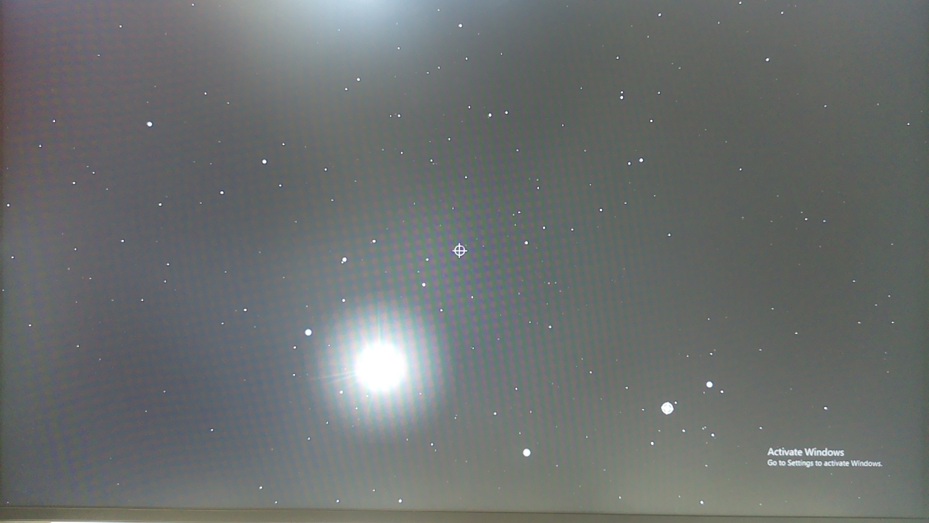
Testing/Images/photo_20250814_171217.jpg
