IvaylooTs/StarTracker/Testing/Images/photo_20250814_171432.jpg

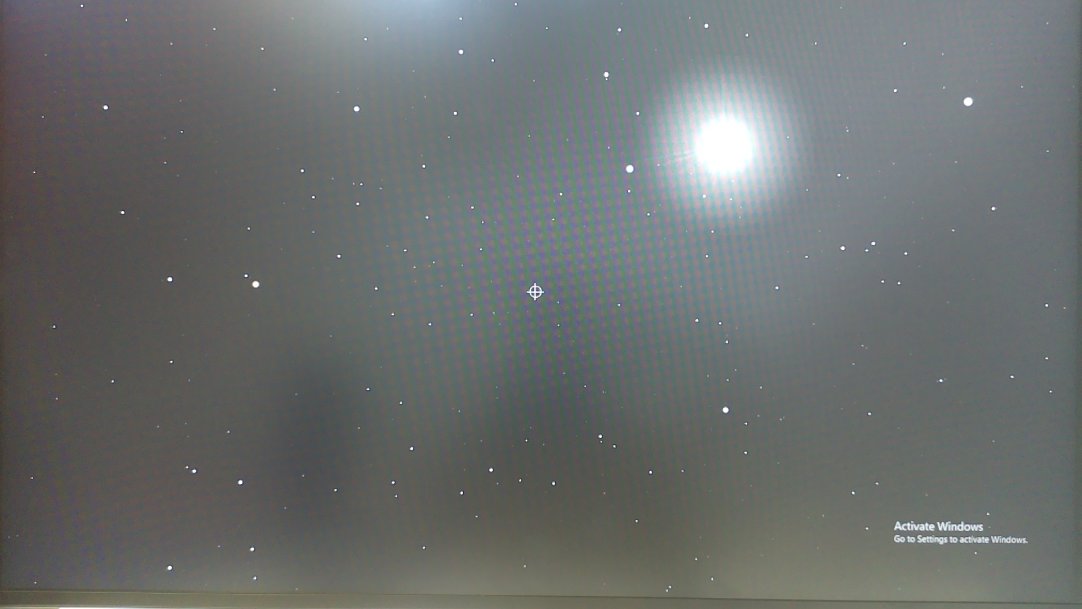
Testing/Images/photo_20250814_171432.jpg
