IvaylooTs/StarTracker/Testing/Images/photo_20250814_171820.jpg

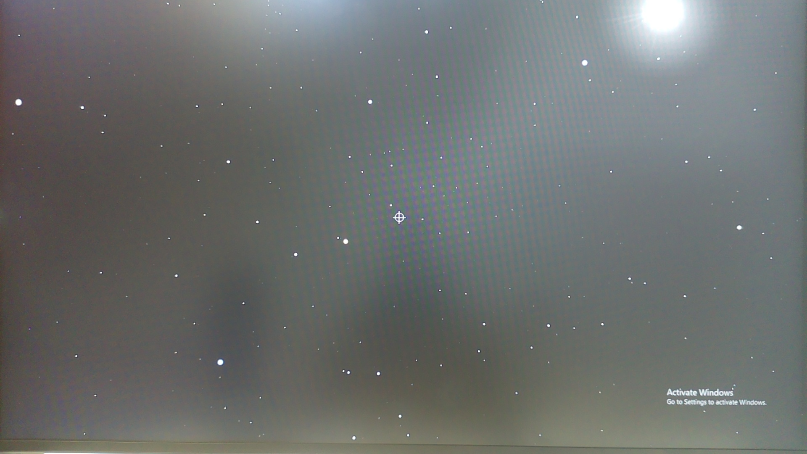
Testing/Images/photo_20250814_171820.jpg
