IvaylooTs/StarTracker/Testing/Images/photo_20250814_173443.jpg

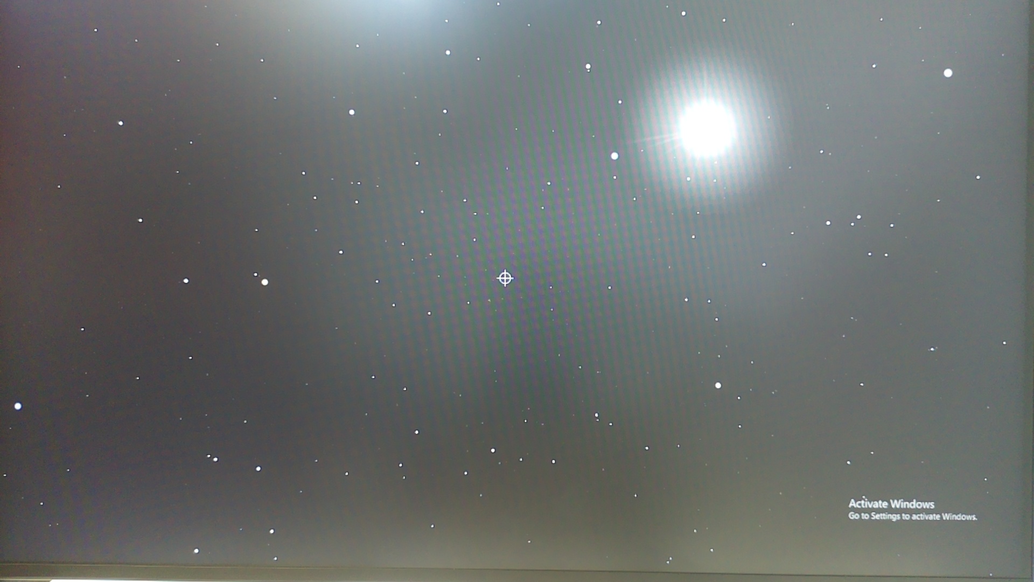
Testing/Images/photo_20250814_173443.jpg
