IvaylooTs/StarTracker/Testing/Images/photo_20250814_173616.jpg

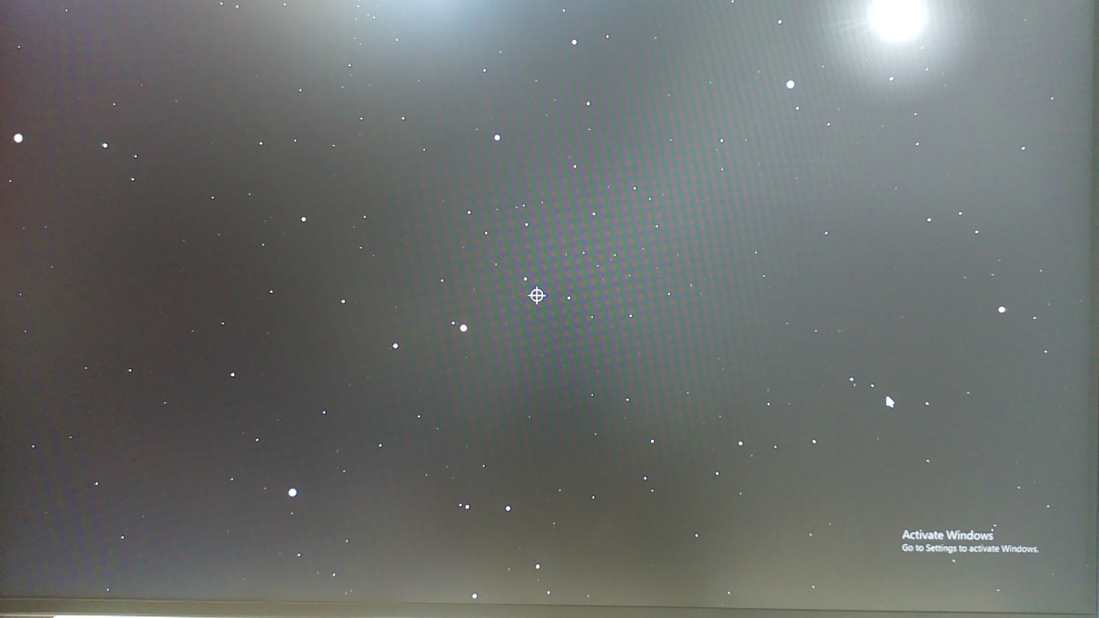
Testing/Images/photo_20250814_173616.jpg
