IvaylooTs/StarTracker/Testing/Images/stars_identified.png

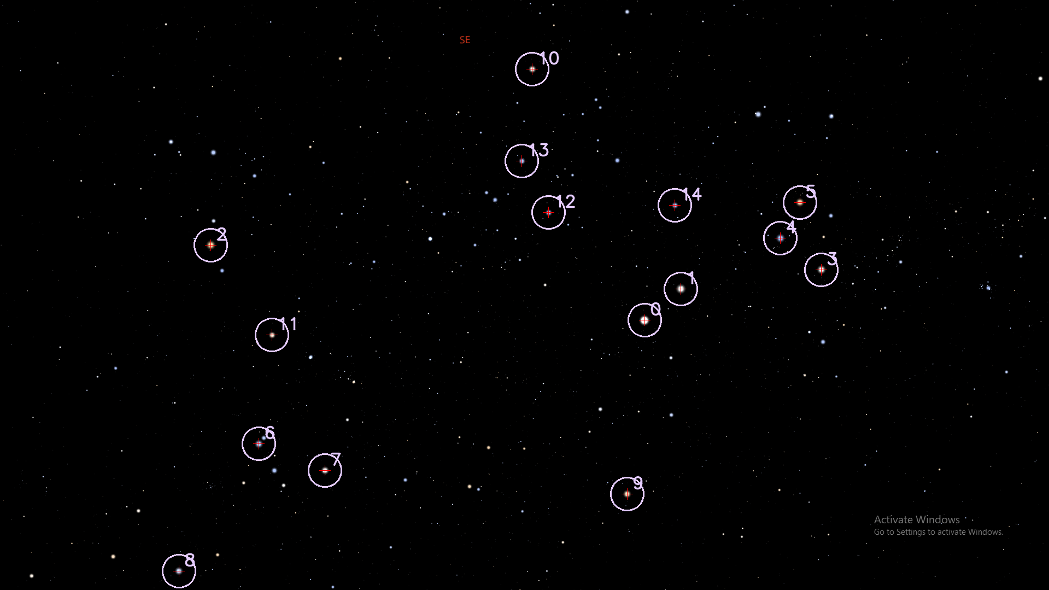
Testing/Images/stars_identified.png
