IvaylooTs/StarTracker/Testing/Images/won'twork.jpg

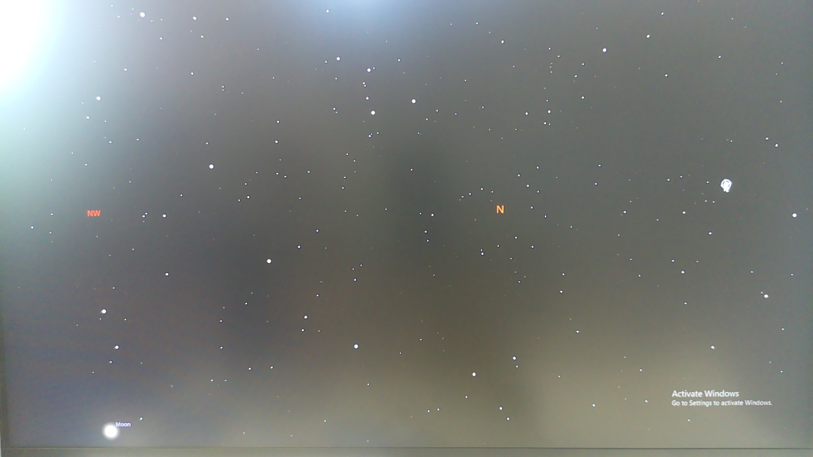
Testing/Images/won'twork.jpg
