IvaylooTs/StarTracker/Testing/Images/work1.jpg

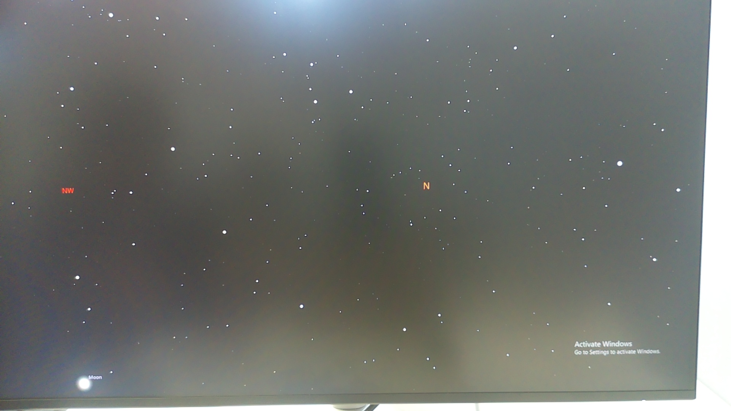
Testing/Images/work1.jpg
