IvaylooTs/StarTracker/Testing/Images/work.jpg

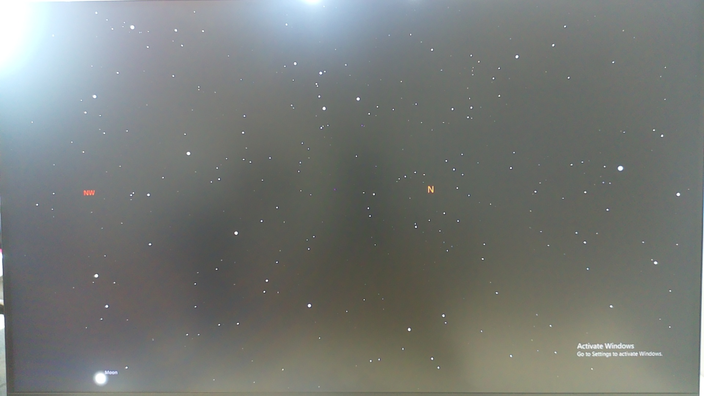
Testing/Images/work.jpg
