IvaylooTs/StarTracker/Testing/Images/WorksSlow.png

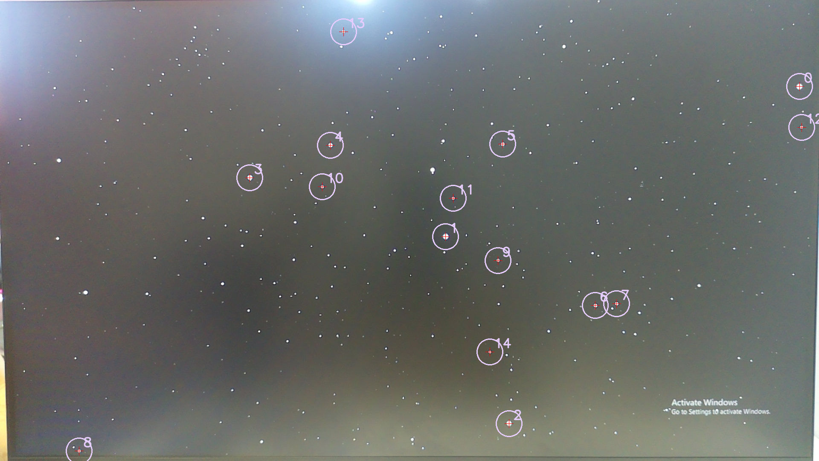
Testing/Images/WorksSlow.png
