IvaylooTs/StarTracker/Testing/performance_by_run.png

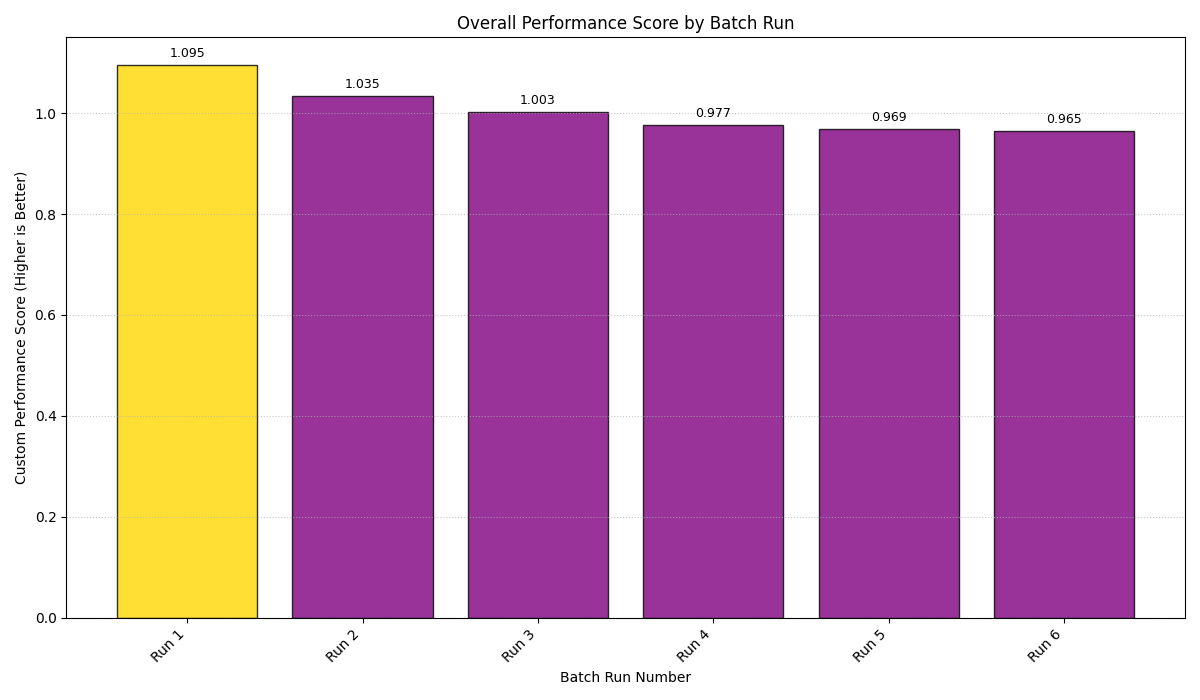
Testing/performance_by_run.png
